polygm/cat_2022/images/5.2사진.jpg

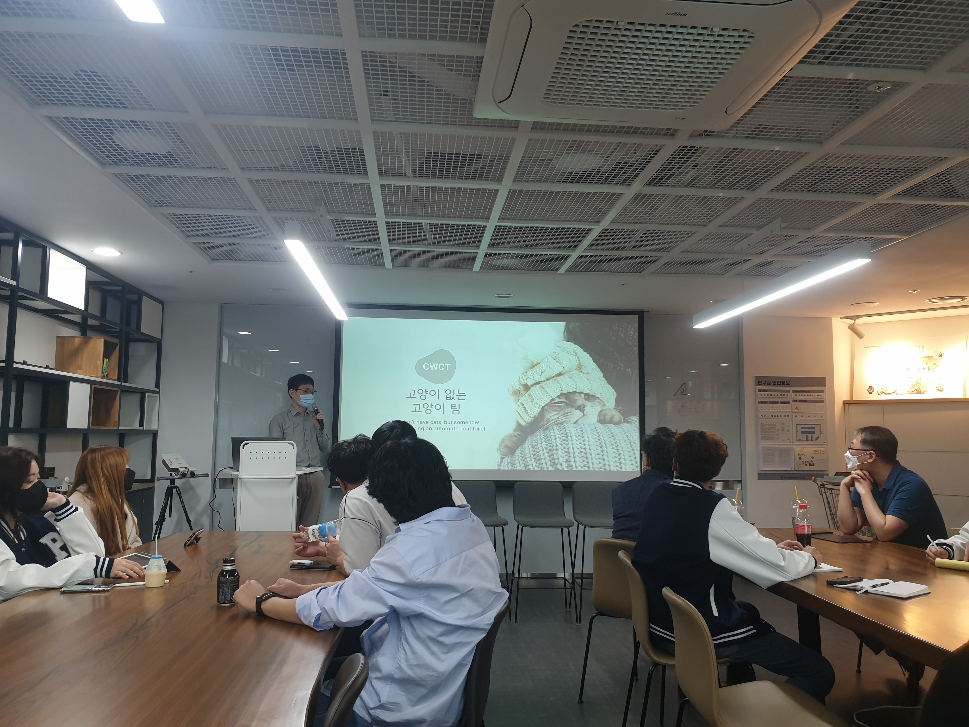
images/5.2사진.jpg
