polygm/cat_2022/images/KakaoTalk_20220418_165429345.png

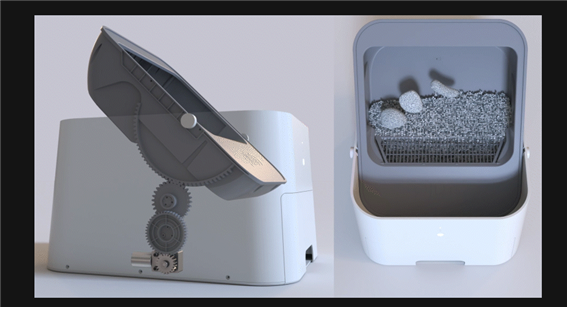
images/KakaoTalk_20220418_165429345.png
