polygm/cat_2022/images/KakaoTalk_20220705_105104796_04.jpg

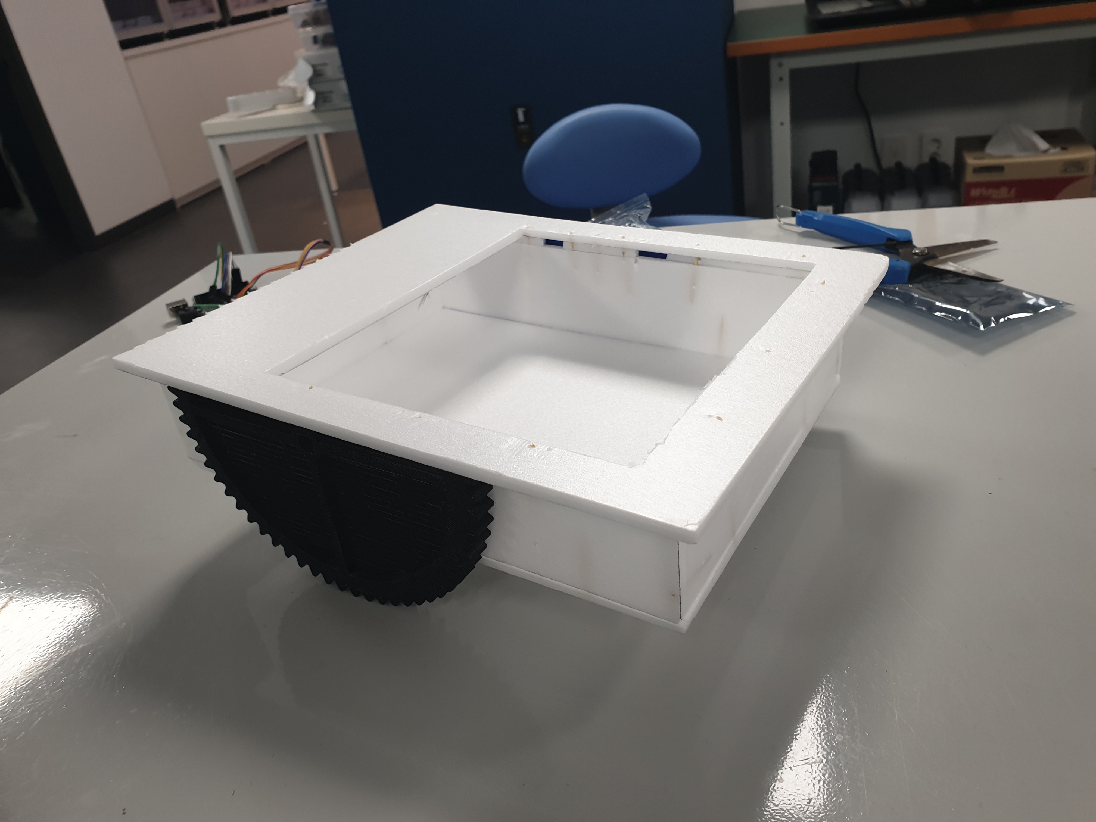
images/KakaoTalk_20220705_105104796_04.jpg
