polygm/cat_2022/images/KakaoTalk_20220705_162518360_03.jpg

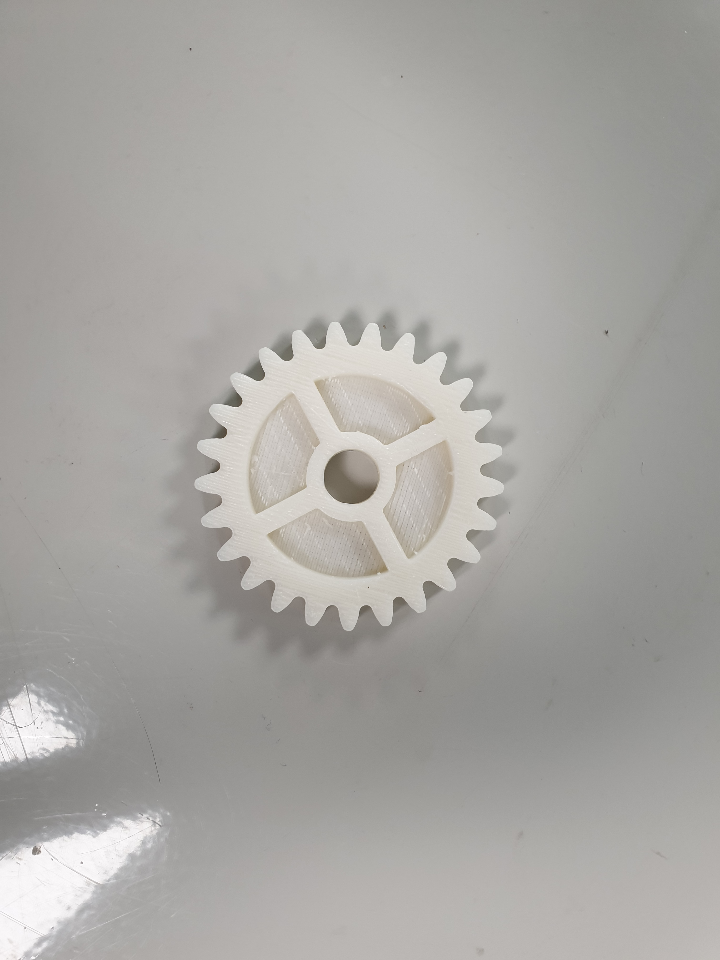
images/KakaoTalk_20220705_162518360_03.jpg
