polygm/cat_2022/images/KakaoTalk_20220920_115222162_04.jpg

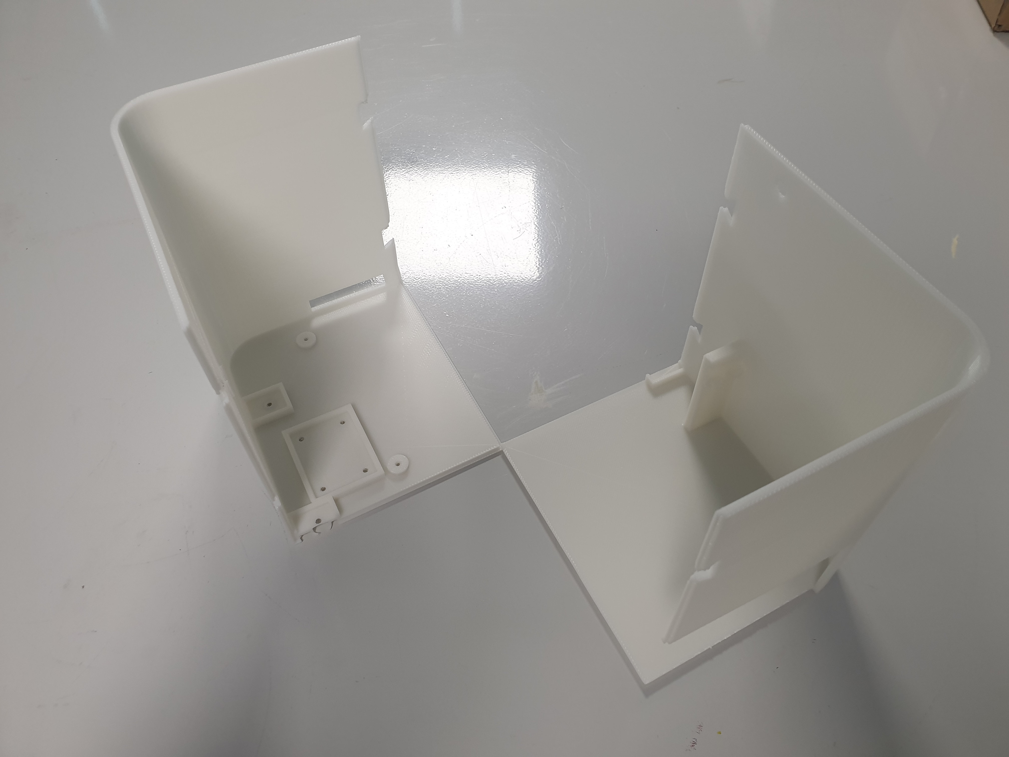
images/KakaoTalk_20220920_115222162_04.jpg
