polygm/cat_2022/images/KakaoTalk_20220922_130827342_01.jpg

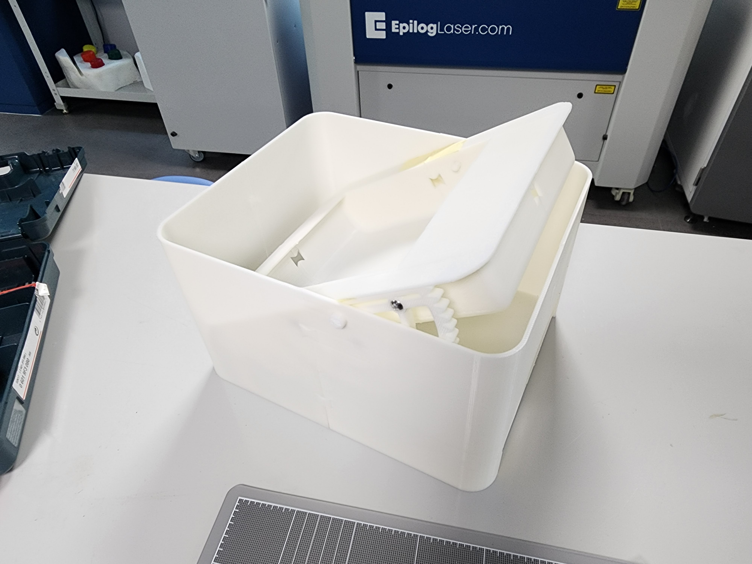
images/KakaoTalk_20220922_130827342_01.jpg
