polygm/cat_2022/images/KakaoTalk_20221005_131710617_01.jpg

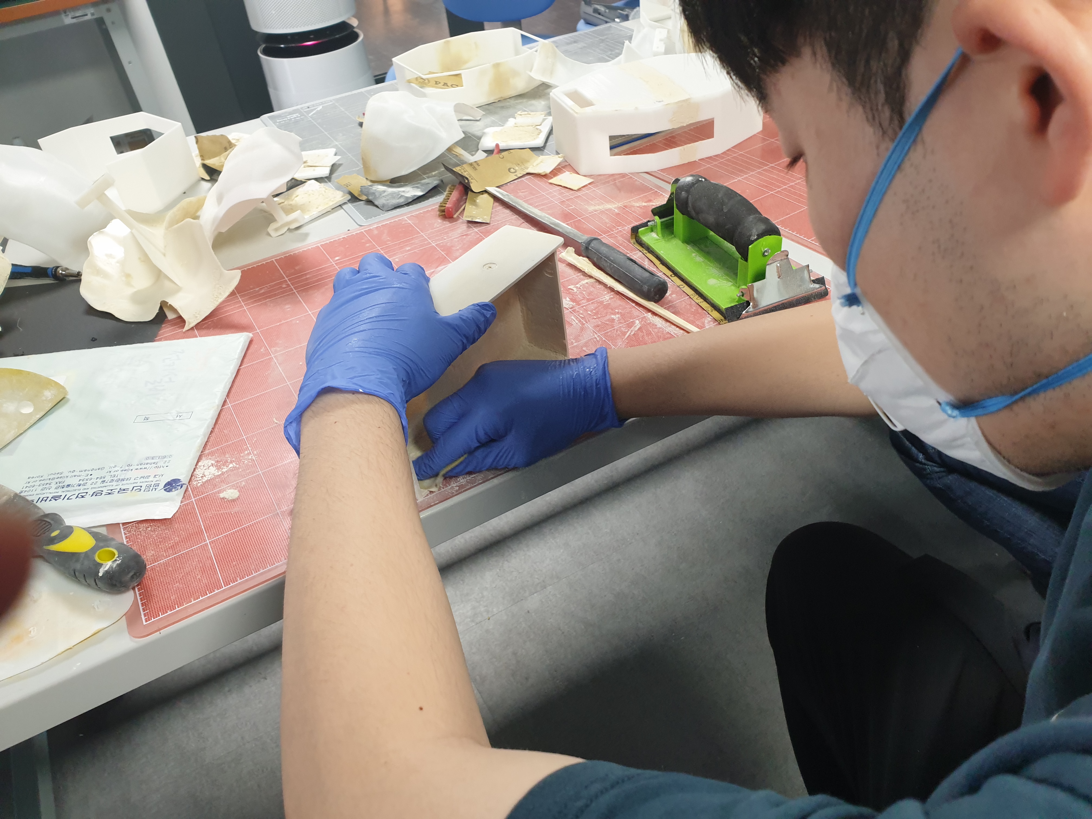
images/KakaoTalk_20221005_131710617_01.jpg
