polygm/cat_2022/images/KakaoTalk_20221005_131710617_03.jpg

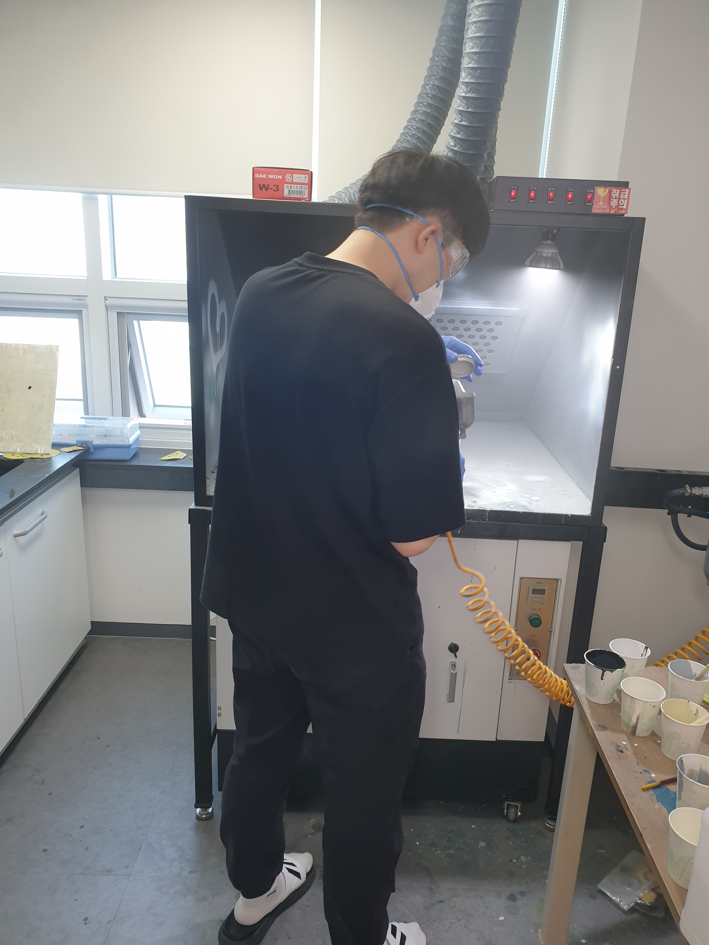
images/KakaoTalk_20221005_131710617_03.jpg
