polygm/cat_2022/images/KakaoTalk_20221005_131710617_04.jpg

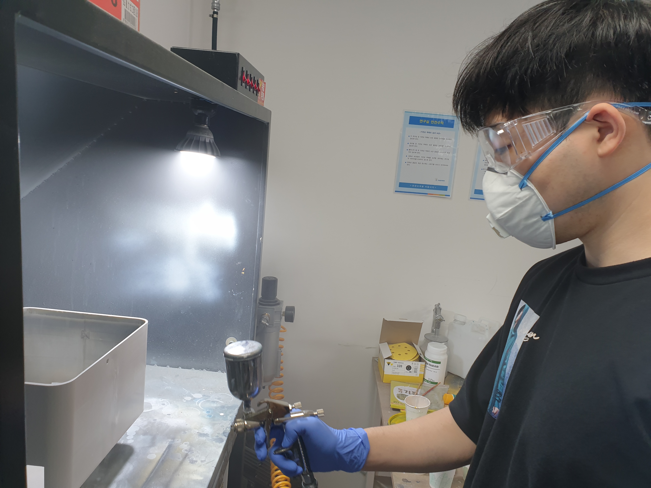
images/KakaoTalk_20221005_131710617_04.jpg
