polygm/cat_2022/images/발표.JPG

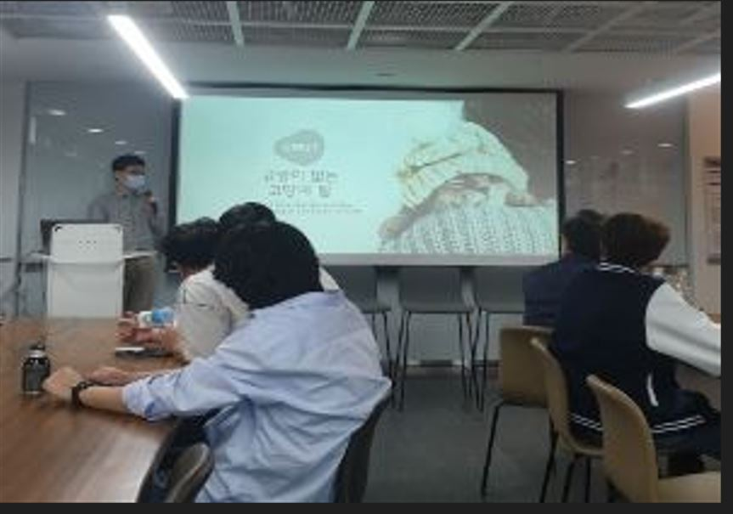
images/발표.JPG
