polygm/cat_2022/images/사전 회의.JPG

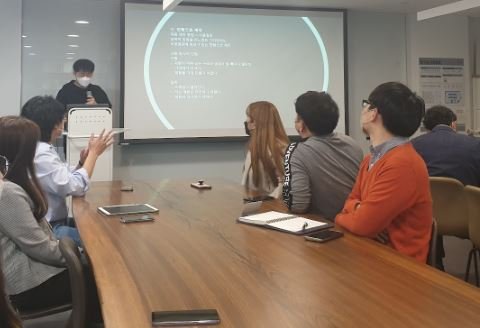
images/사전 회의.JPG
