polygm/cat_2022/images/사전.JPG

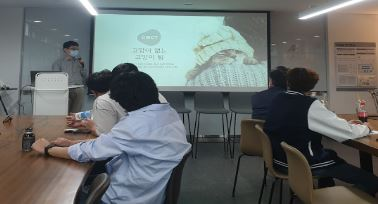
images/사전.JPG
