polygm/cat_2022/images/첫 모형 제작.jpg

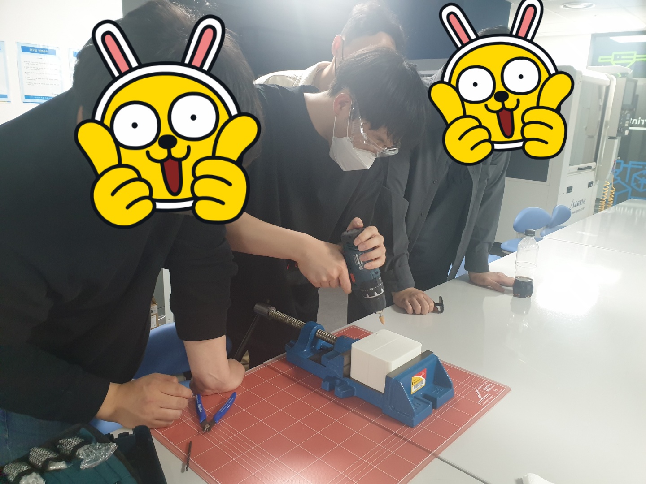
images/첫 모형 제작.jpg
