polygm/cat_2022/modeling/0.JPG

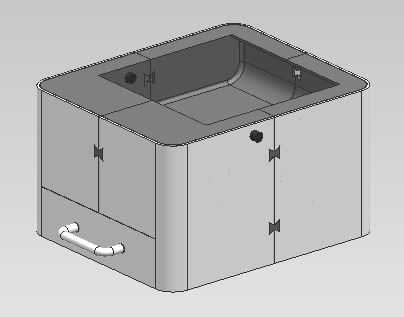
modeling/0.JPG
