polygm/cat_2022/modeling/CWCT특장점.JPG

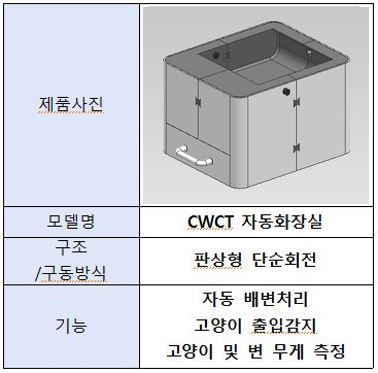
modeling/CWCT특장점.JPG
