polygm/cat_2022/modeling/고양이 분해도.png

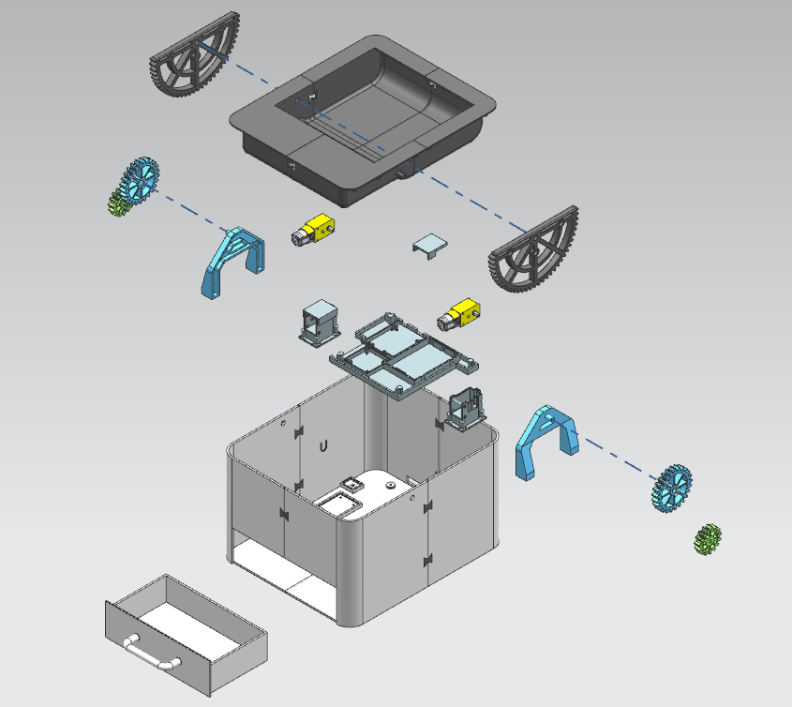
modeling/고양이 분해도.png
