polygm/cat_2022/modeling/기어1.JPG

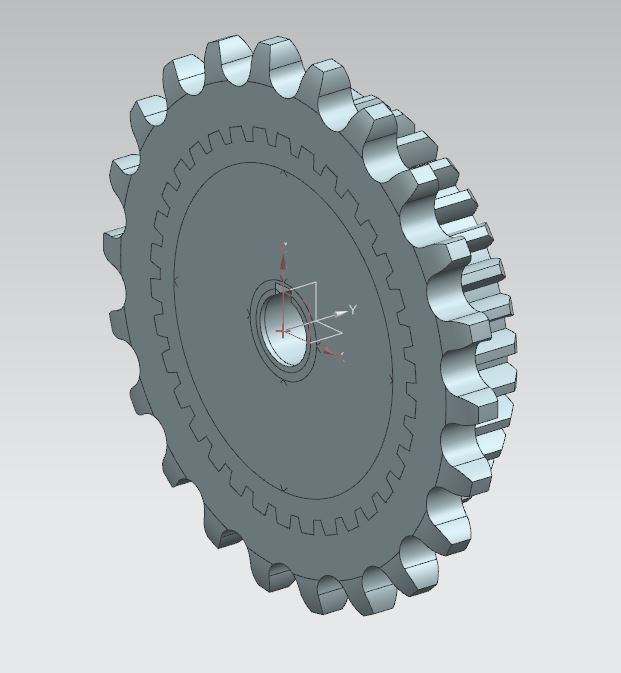
modeling/기어1.JPG
