polygm/cat_2022/modeling/기어2.JPG

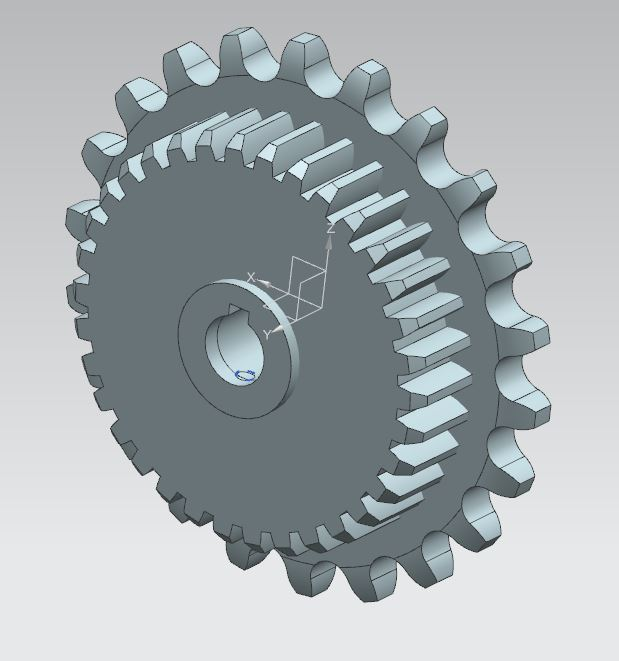
modeling/기어2.JPG
