polygm/cat_2022/modeling/기어3.JPG

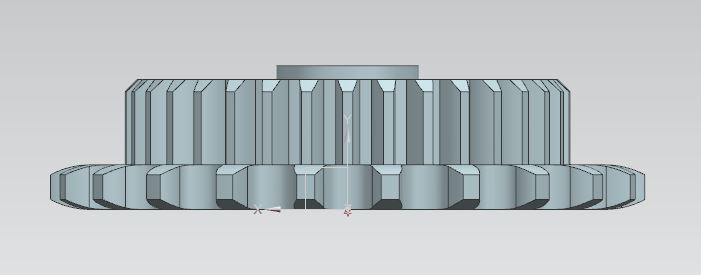
modeling/기어3.JPG
