polygm/cat_2022/modeling/기어4.JPG

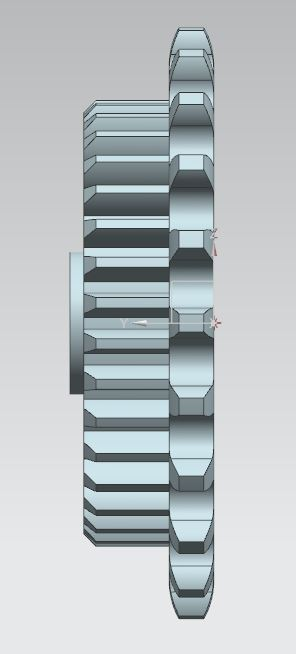
modeling/기어4.JPG
