polygm/cat_2022/modeling/모래통 기어.JPG

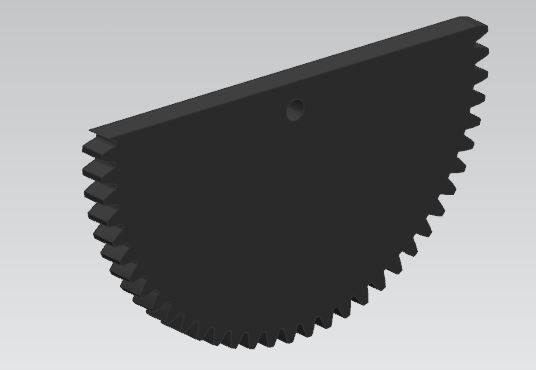
modeling/모래통 기어.JPG
