polygm/cat_2022/modeling/모래통 드래프팅.JPG

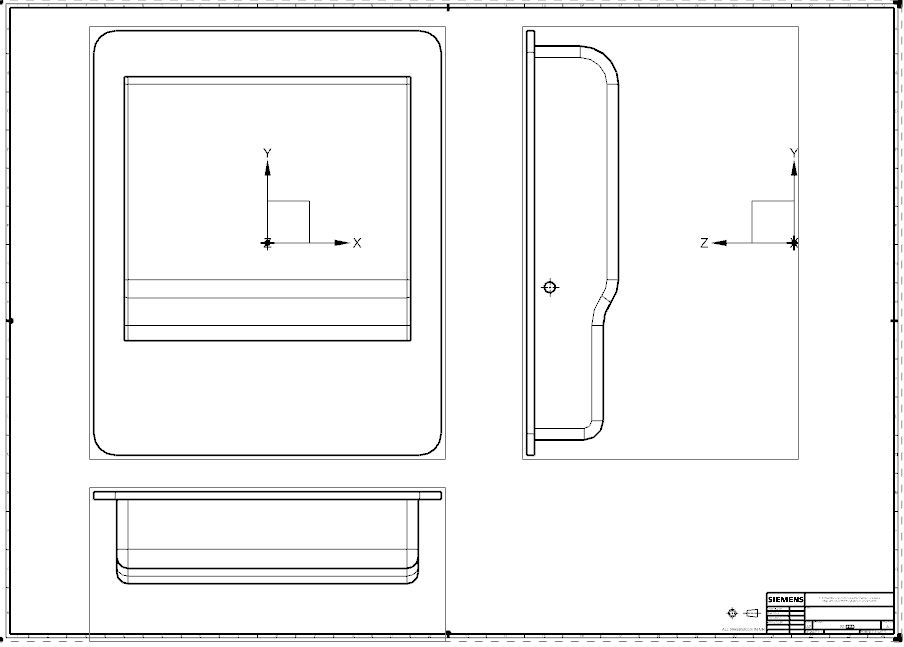
modeling/모래통 드래프팅.JPG
