polygm/cat_2022/modeling/본체 드래프팅.JPG

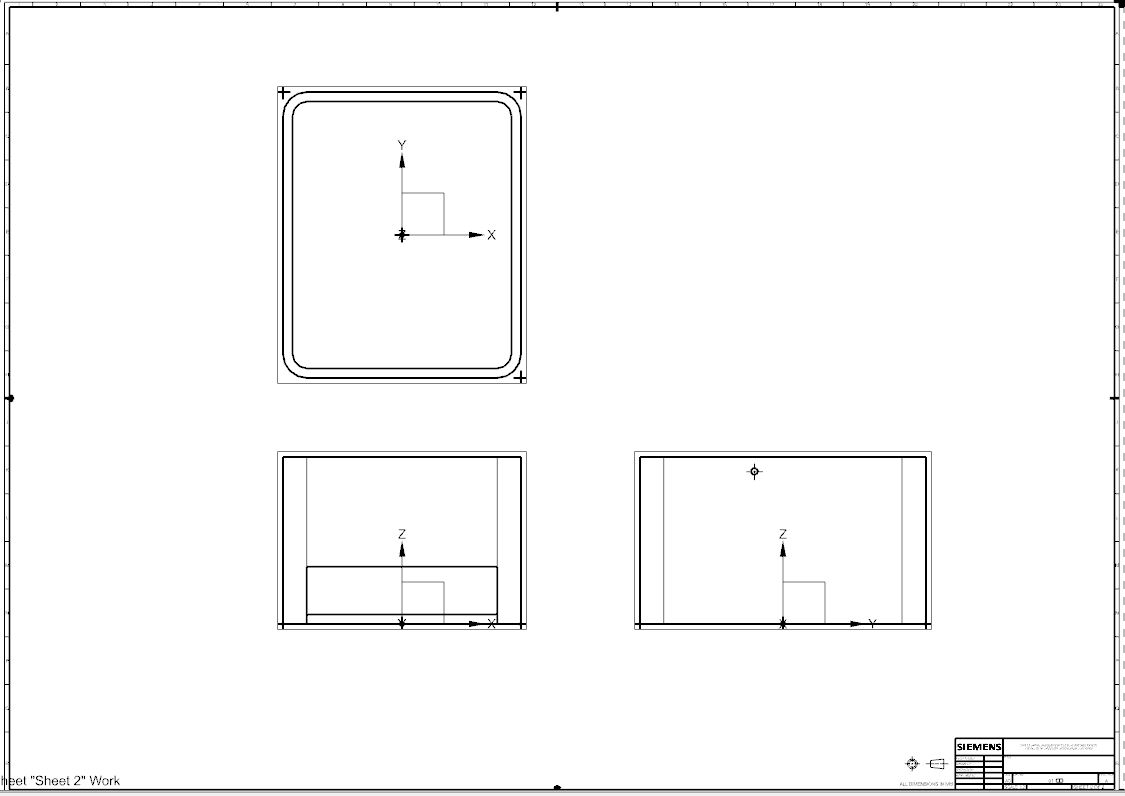
modeling/본체 드래프팅.JPG
