polygm/cat_2022/modeling/완성품1.png

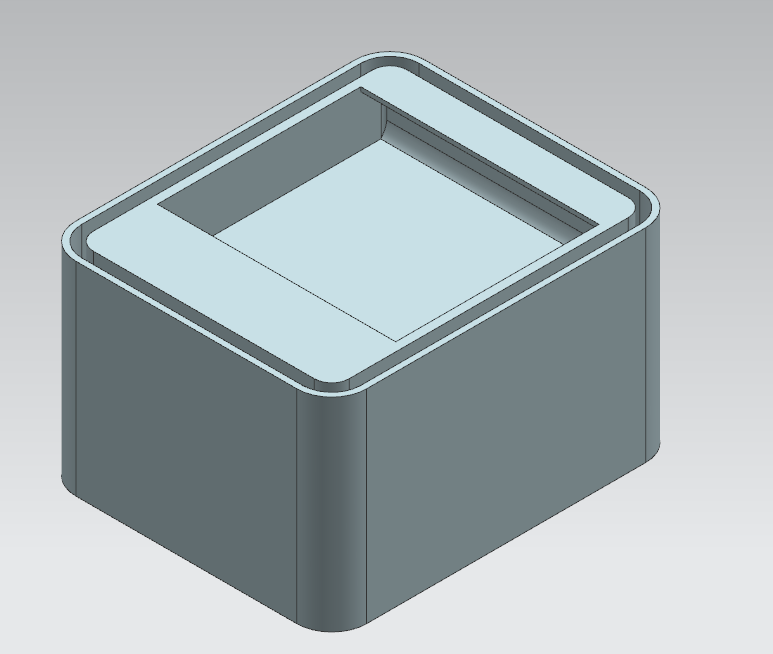
modeling/완성품1.png
