polygm/cat_2022/modeling/완성품2.png

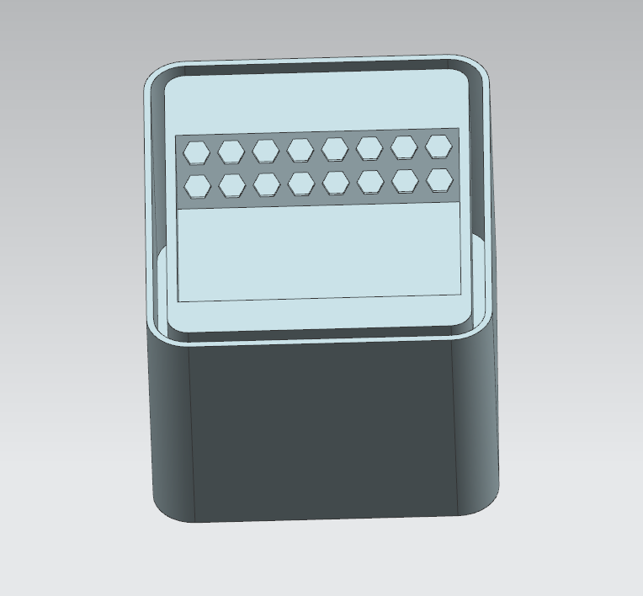
modeling/완성품2.png
