polygm/cat_2022/modeling/컴포넌트/ㅇ/Ultrasonic Sensor HC-SR04/Ultrasonic Sensor HC-SR04 2.jpg

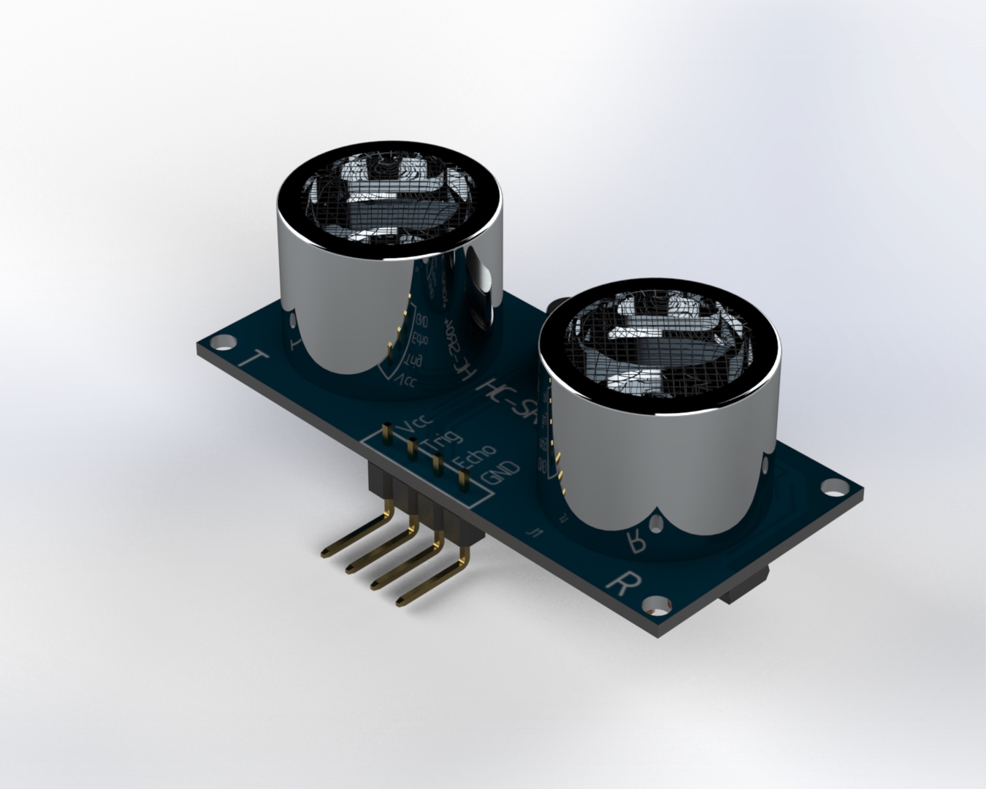
modeling/컴포넌트/ㅇ/Ultrasonic Sensor HC-SR04/Ultrasonic Sensor HC-SR04 2.jpg
