polygm/cat_2022/modeling/컴포넌트/두견/foto_4.png

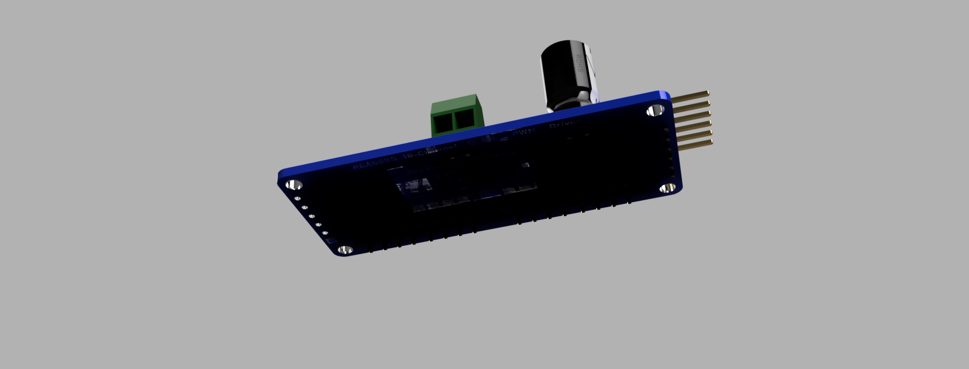
modeling/컴포넌트/두견/foto_4.png
