polygm/cat_2022/modeling/화장실 작동 순서 사진/2.JPG

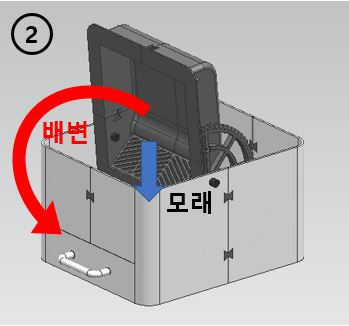
modeling/화장실 작동 순서 사진/2.JPG
