polygm/cat_2022/modeling/회전부.png

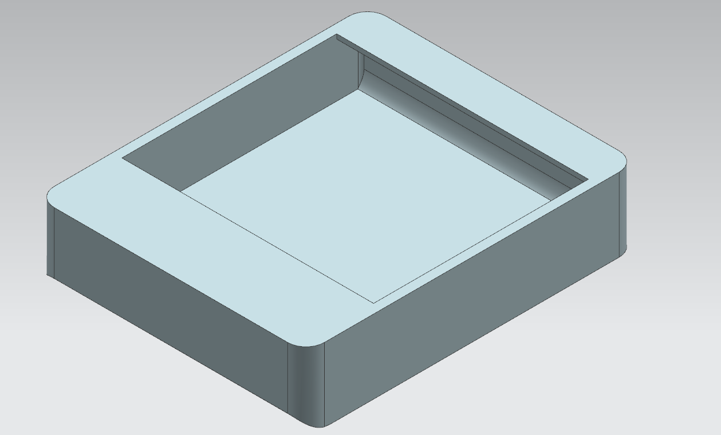
modeling/회전부.png
