polygm/cat_2022/product/KakaoTalk_20221005_114139845.jpg

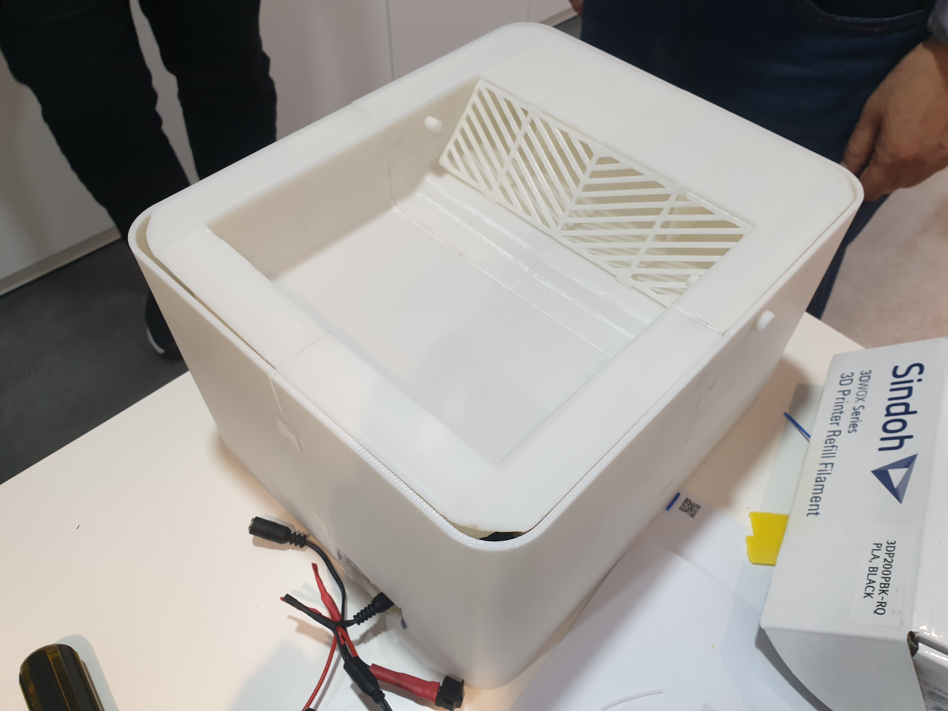
product/KakaoTalk_20221005_114139845.jpg
