polygm/cat_2022/product/KakaoTalk_20221005_131516674_01.jpg

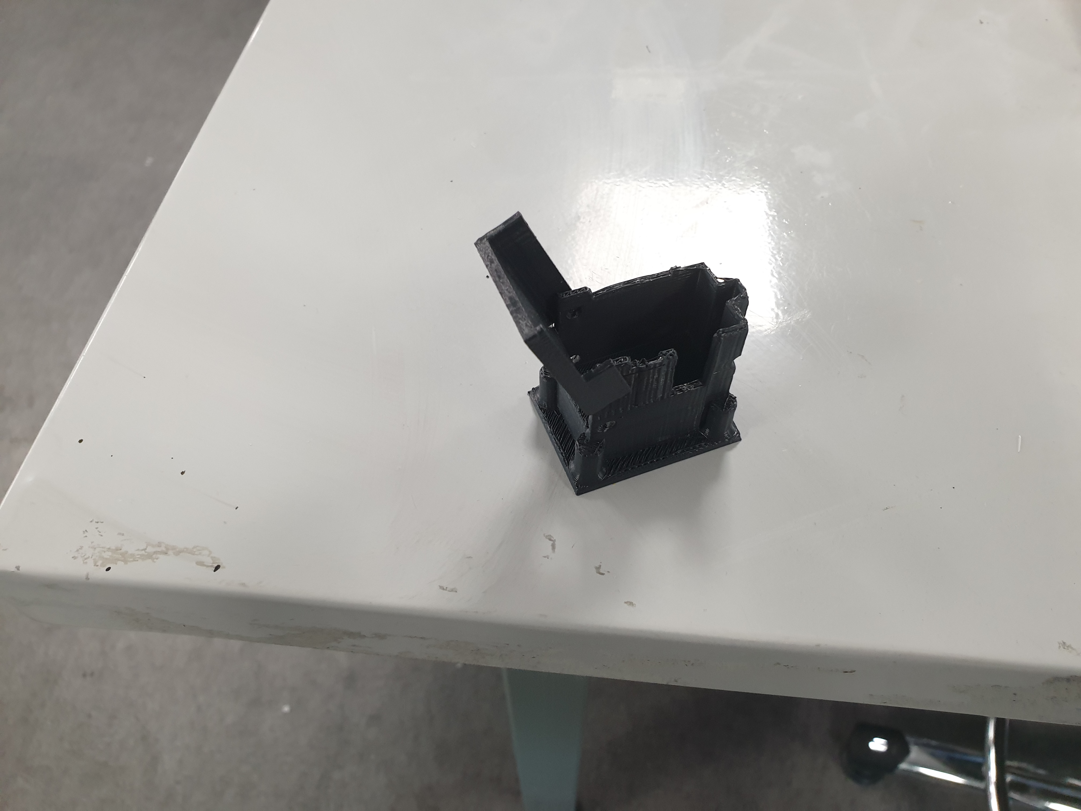
product/KakaoTalk_20221005_131516674_01.jpg
