polygm/cat_2022/product/KakaoTalk_20221005_131516674_02.jpg

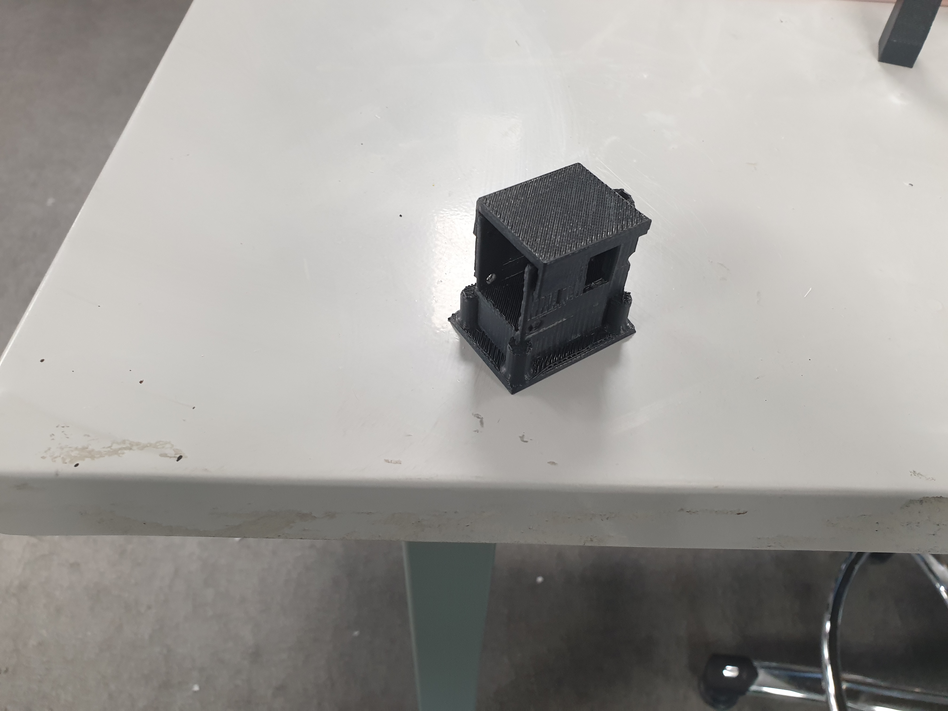
product/KakaoTalk_20221005_131516674_02.jpg
