polygm/cat_2022/product/KakaoTalk_20221005_131516674_05.jpg

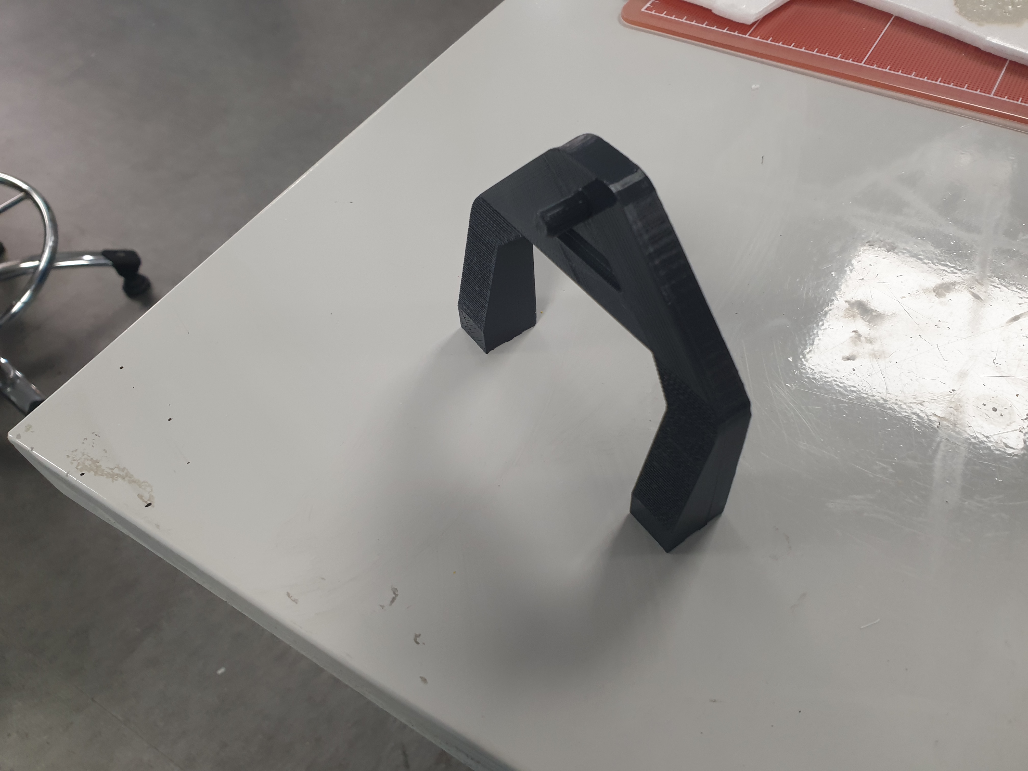
product/KakaoTalk_20221005_131516674_05.jpg
