polygm/cat_2022/product/KakaoTalk_20221005_131516674_07.jpg

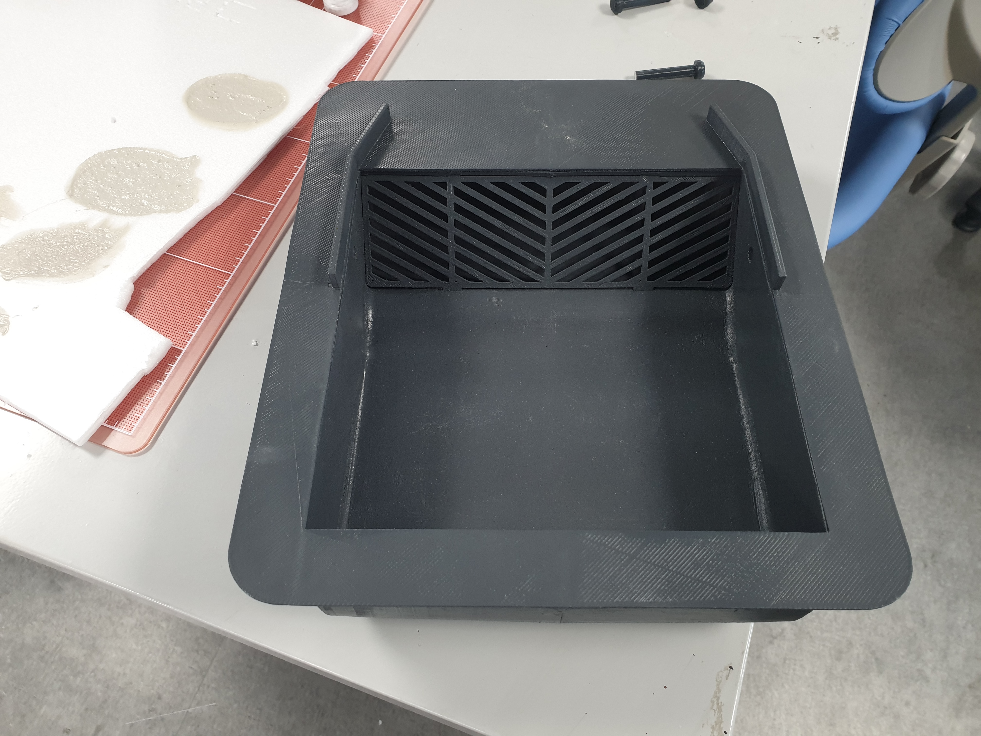
product/KakaoTalk_20221005_131516674_07.jpg
