polygm/cat_2022/research/4.JPG

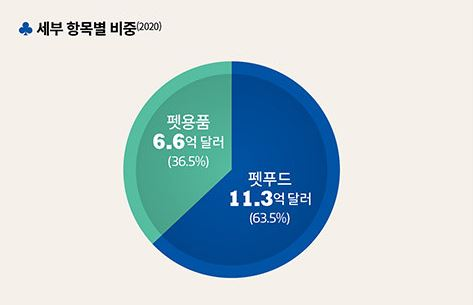
research/4.JPG
