polygm/cat_2022/research/5.JPG

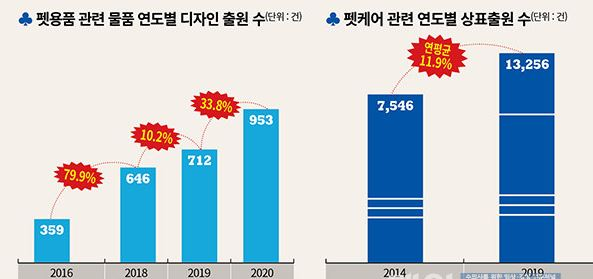
research/5.JPG
