polygm/cat_2022/research/7.JPG

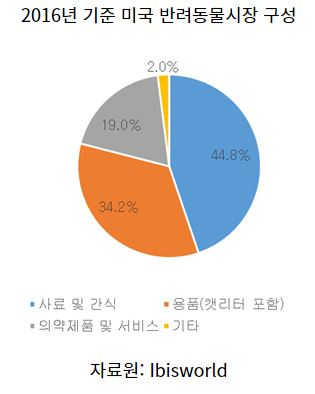
research/7.JPG
