polygm/cat_2022/research/8.JPG

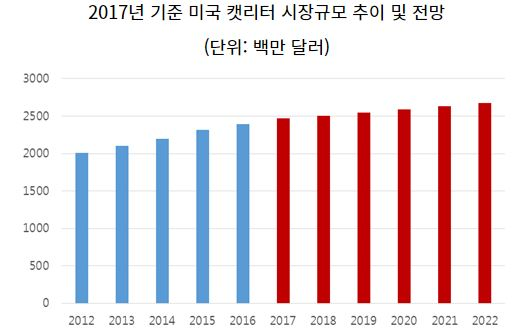
research/8.JPG
