polygm/cat_2022/research/3213.JPG

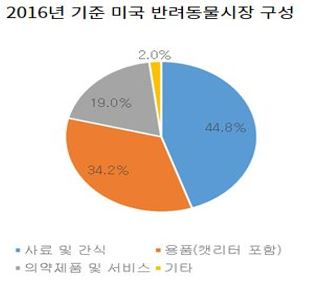
research/3213.JPG
