polygm/cat_2022/research/cheap.JPG

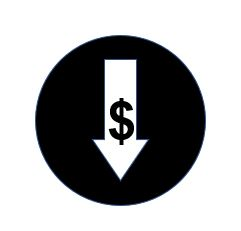
research/cheap.JPG
