polygm/cat_2022/research/cheaper.JPG

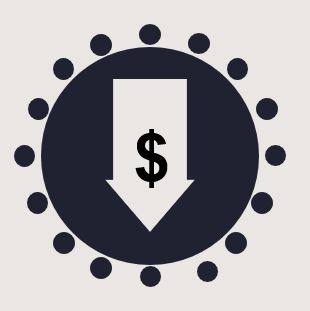
research/cheaper.JPG
