polygm/cat_2022/research/g.jpg

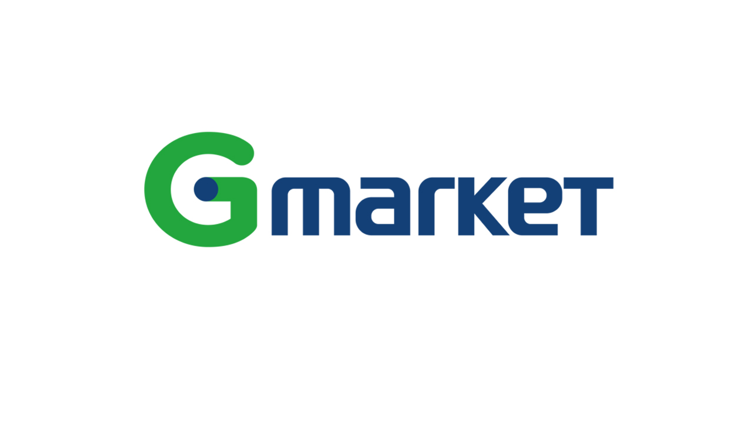
research/g.jpg
