polygm/cat_2022/research/gg.jpg

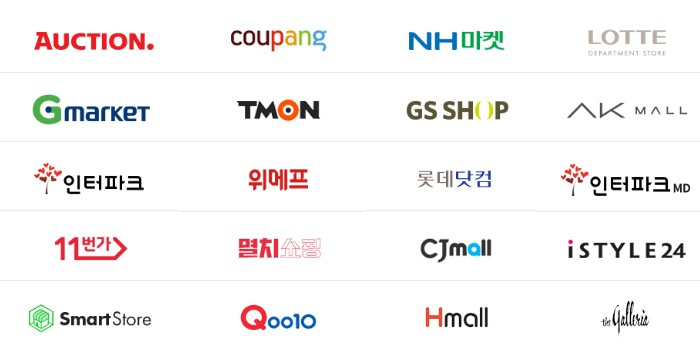
research/gg.jpg
