polygm/cat_2022/research/KakaoTalk_20220704_164942398.jpg

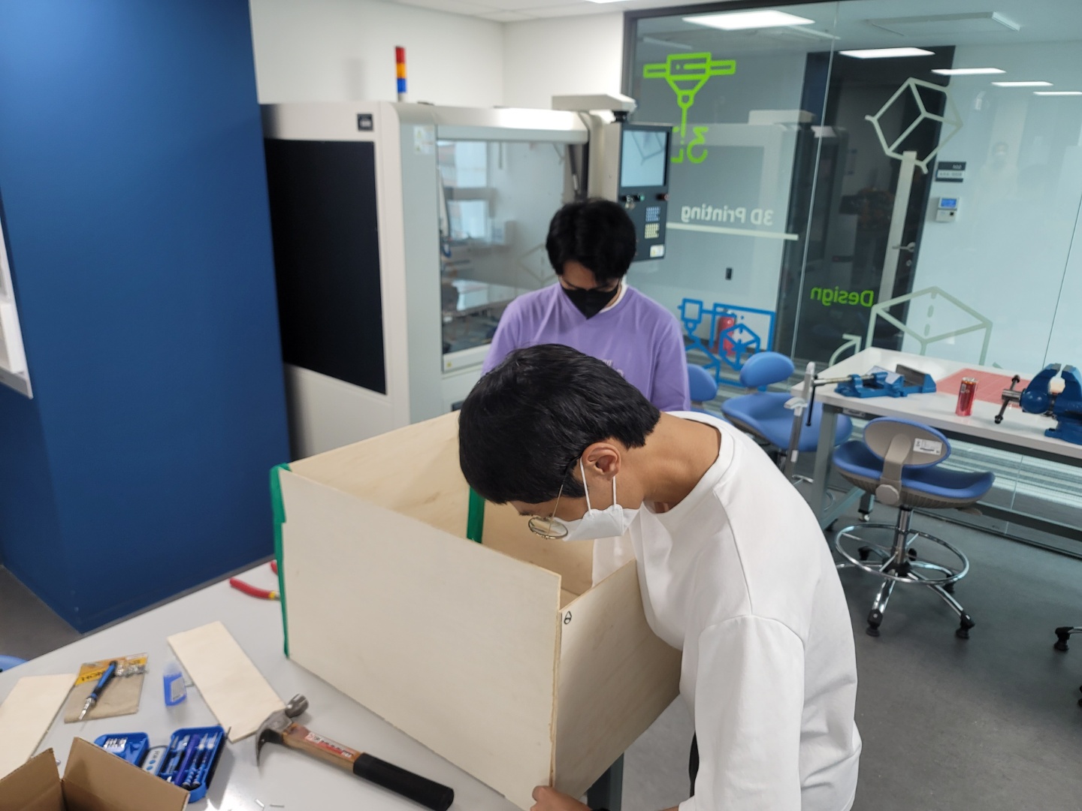
research/KakaoTalk_20220704_164942398.jpg
