polygm/cat_2022/research/KakaoTalk_20220920_115222162_03.jpg

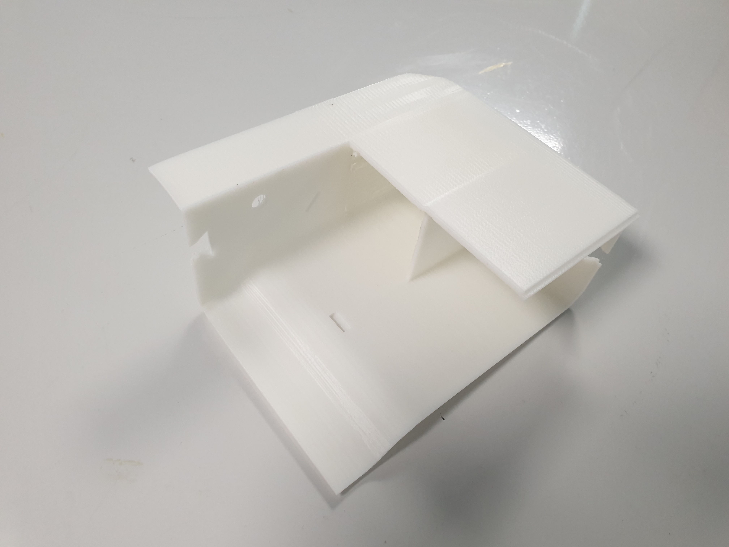
research/KakaoTalk_20220920_115222162_03.jpg
