polygm/cat_2022/research/KakaoTalk_20220922_152420083.png

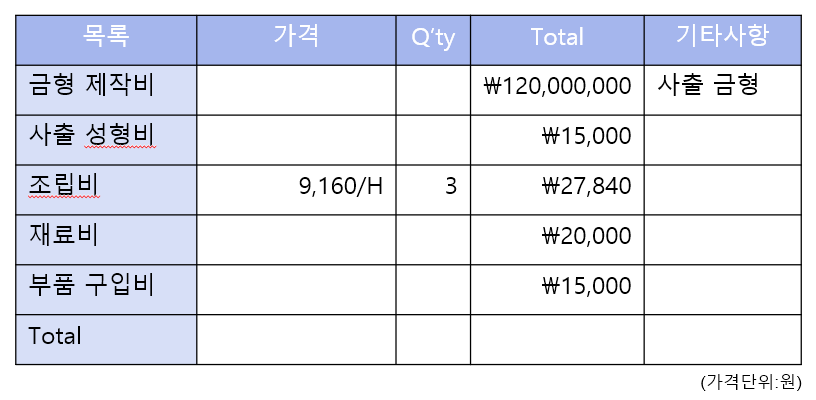
research/KakaoTalk_20220922_152420083.png
