polygm/cat_2022/research/s.JPG

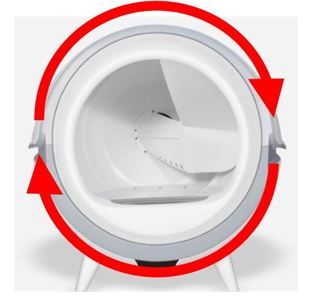
research/s.JPG
