polygm/cat_2022/research/Untitled-1.png

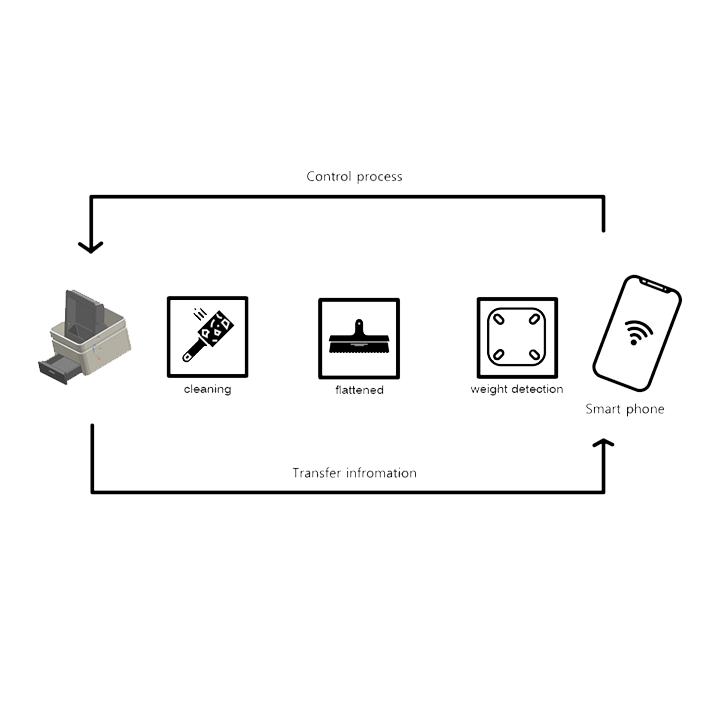
research/Untitled-1.png
