polygm/cat_2022/research/wifi모듈.JPG

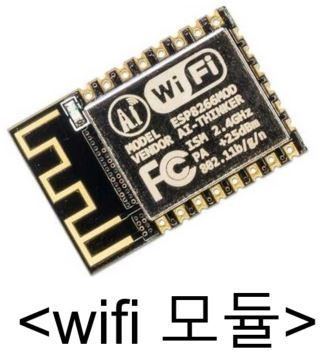
research/wifi모듈.JPG
