polygm/cat_2022/research/ㄴ.JPG

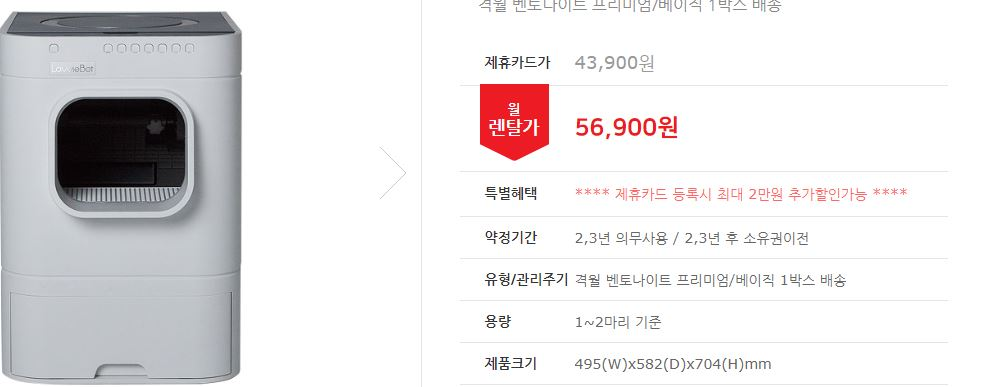
research/ㄴ.JPG
