polygm/cat_2022/research/개선.JPG

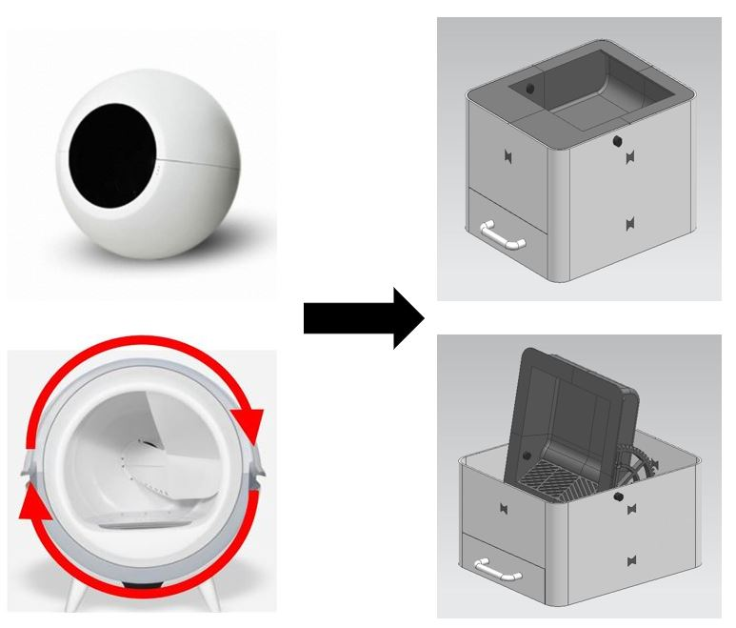
research/개선.JPG
