polygm/cat_2022/research/고양2.JPG

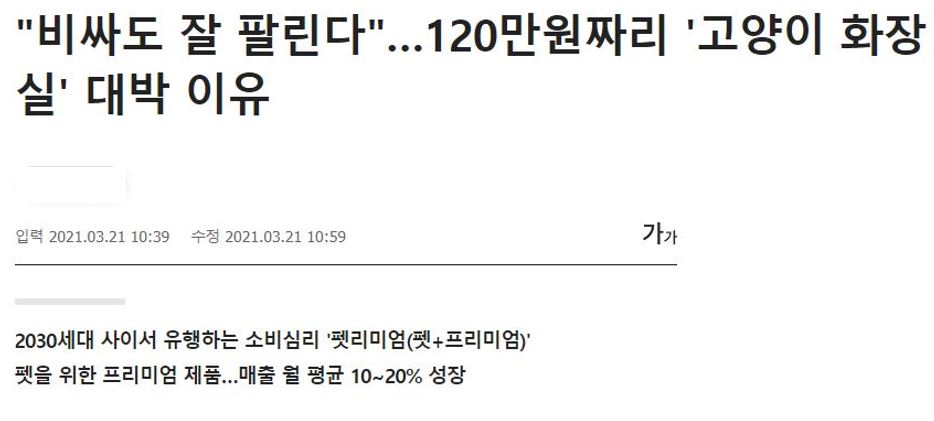
research/고양2.JPG
