polygm/cat_2022/research/고양.JPG

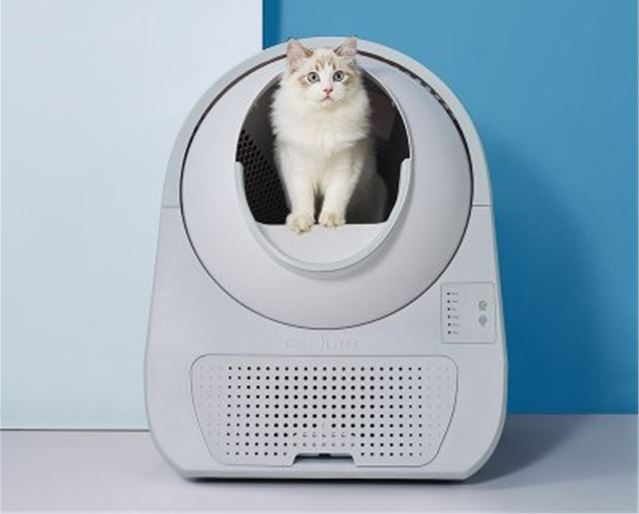
research/고양.JPG
