polygm/cat_2022/research/고양이2.jpg

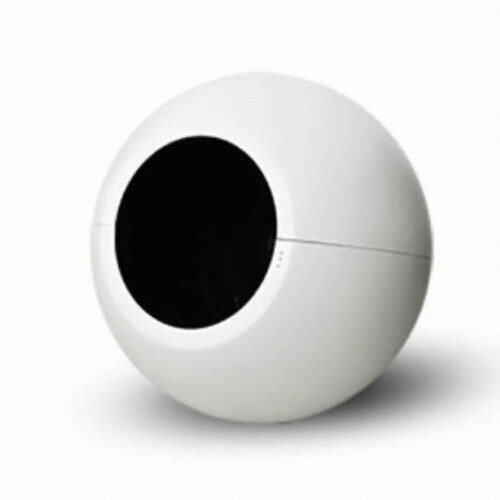
research/고양이2.jpg
