polygm/cat_2022/research/고양이 무게2.JPG

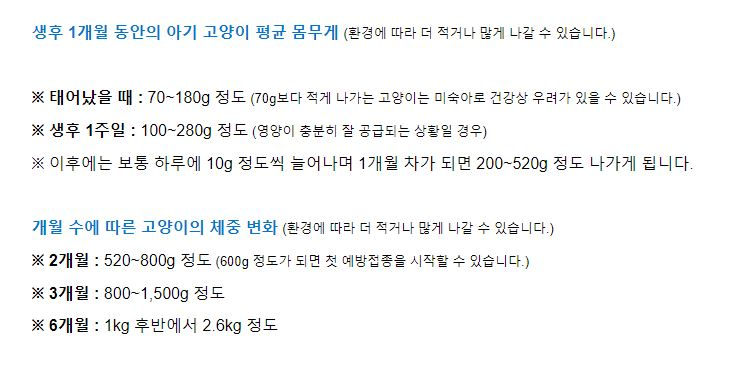
research/고양이 무게2.JPG
