polygm/cat_2022/research/고양이 시장2.JPG

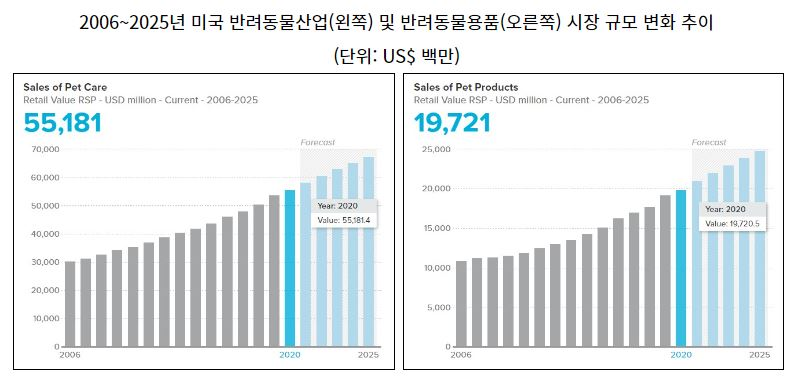
research/고양이 시장2.JPG
