polygm/cat_2022/research/고양이 시장규모.JPG

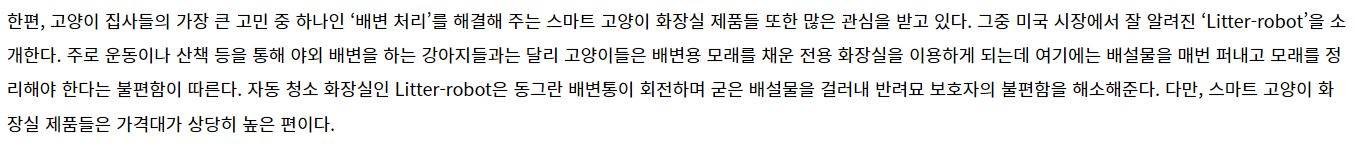
research/고양이 시장규모.JPG
