polygm/cat_2022/research/고양이 평균 무게.JPG

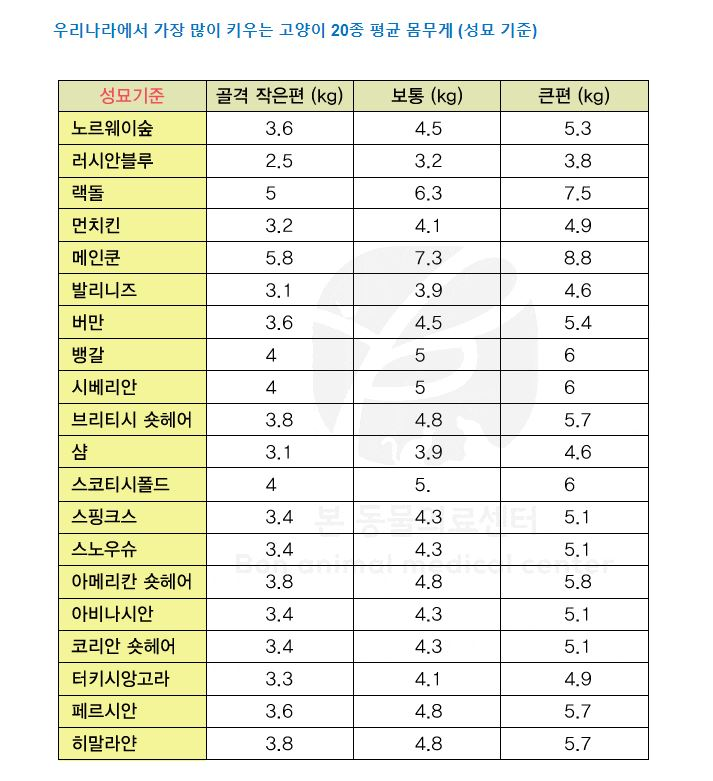
research/고양이 평균 무게.JPG
