polygm/cat_2022/research/구동도.JPG

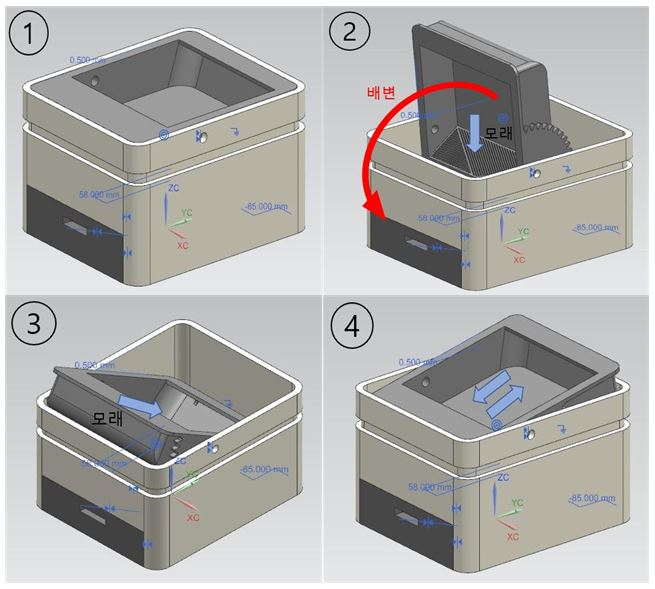
research/구동도.JPG
