polygm/cat_2022/research/구성도 완성.jpg

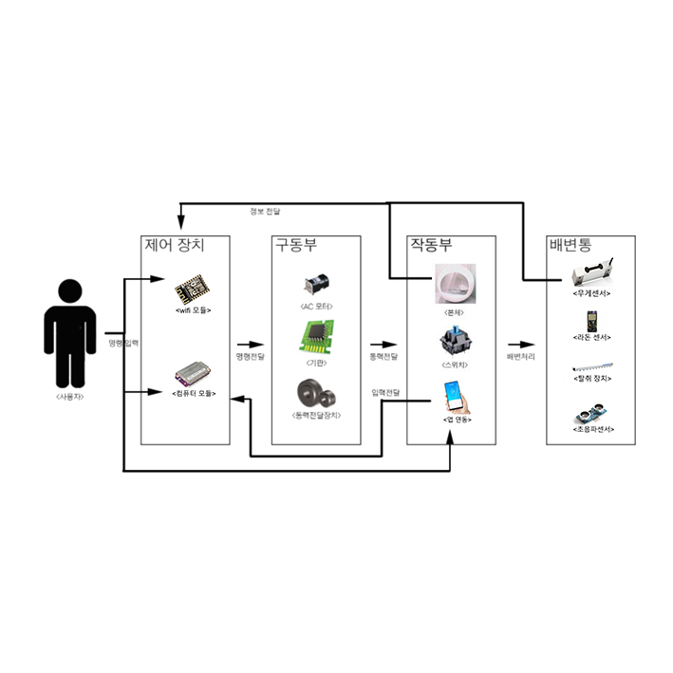
research/구성도 완성.jpg
