polygm/cat_2022/research/기능 흐름도.JPG

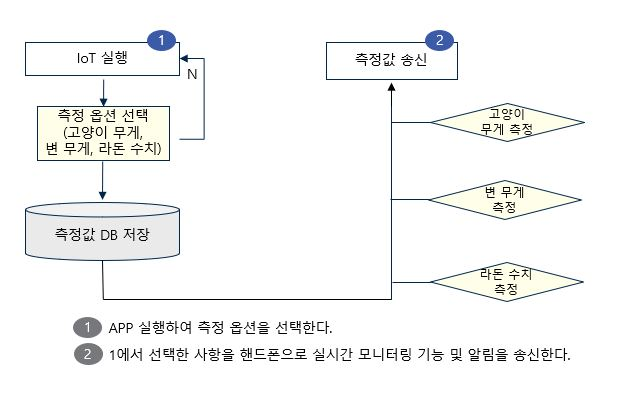
research/기능 흐름도.JPG
