polygm/cat_2022/research/기능처리.JPG

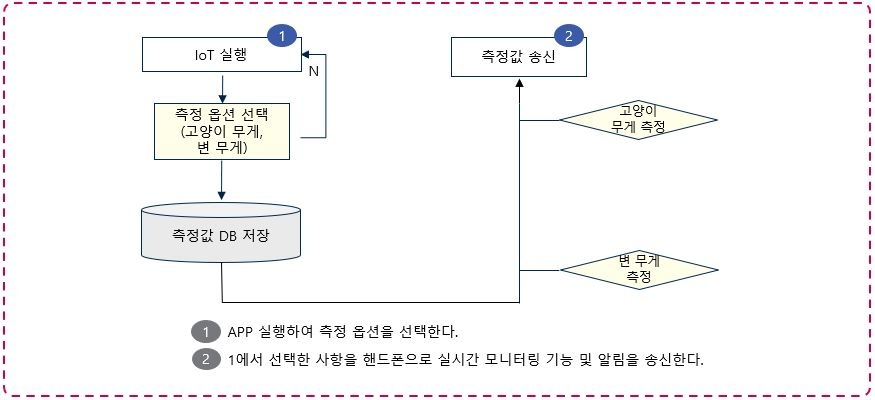
research/기능처리.JPG
