polygm/cat_2022/research/기어 설명.JPG

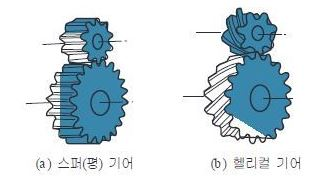
research/기어 설명.JPG
