polygm/cat_2022/research/냥장실 비교.JPG

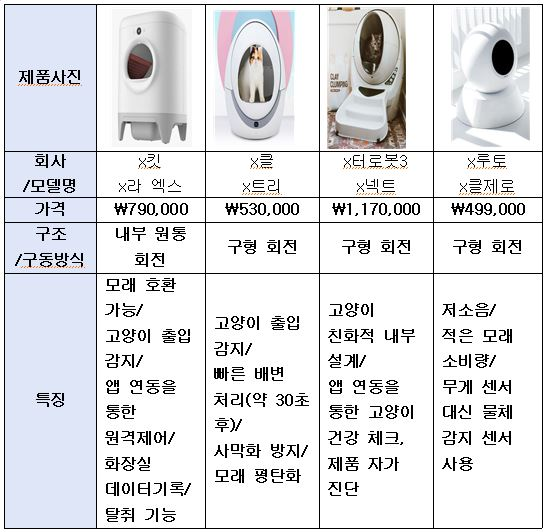
research/냥장실 비교.JPG
