polygm/cat_2022/research/라돈 센서.JPG

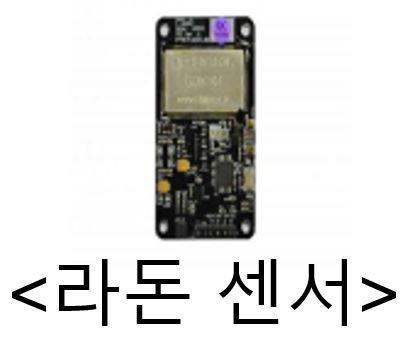
research/라돈 센서.JPG
