polygm/cat_2022/research/라돈센서.JPG

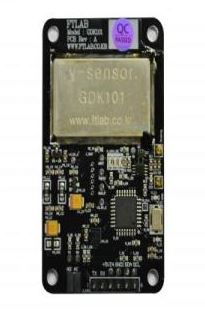
research/라돈센서.JPG
