polygm/cat_2022/research/모터 차이.JPG

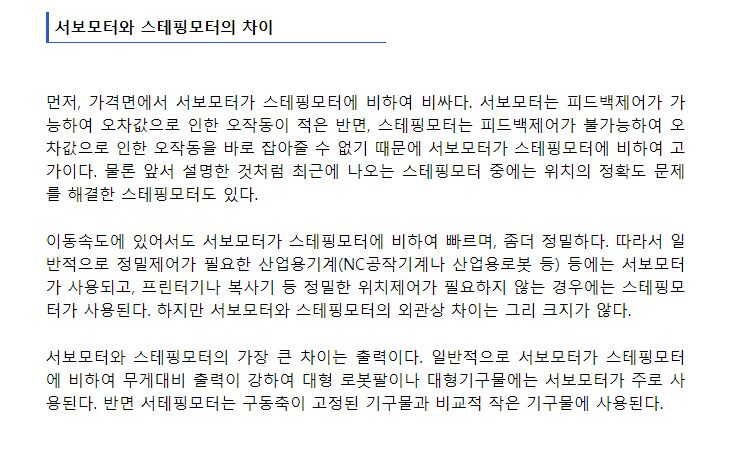
research/모터 차이.JPG
