polygm/cat_2022/research/모터.JPG

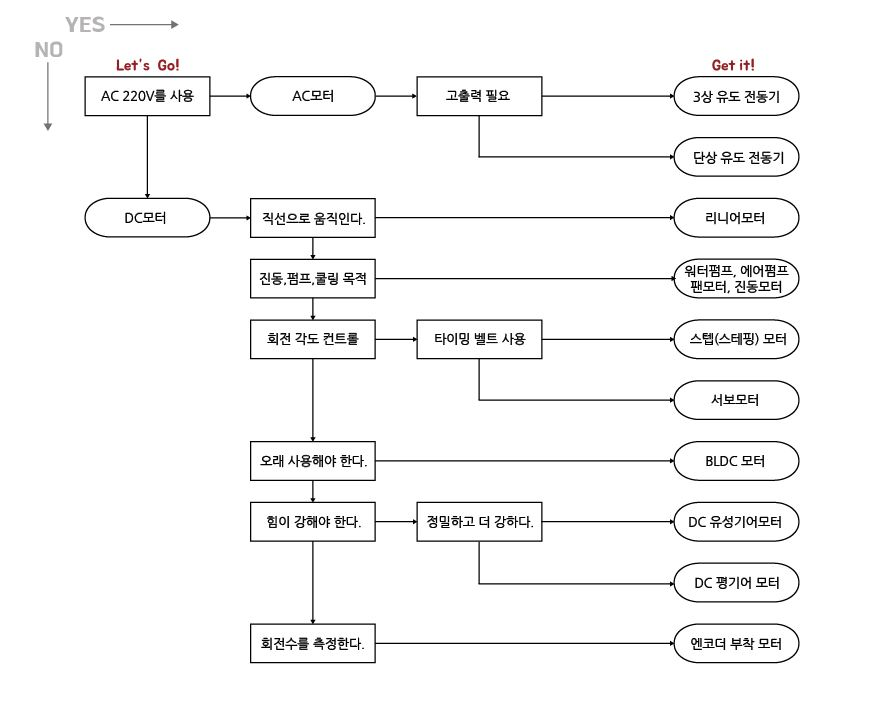
research/모터.JPG
