polygm/cat_2022/research/무게 센서 사진.JPG

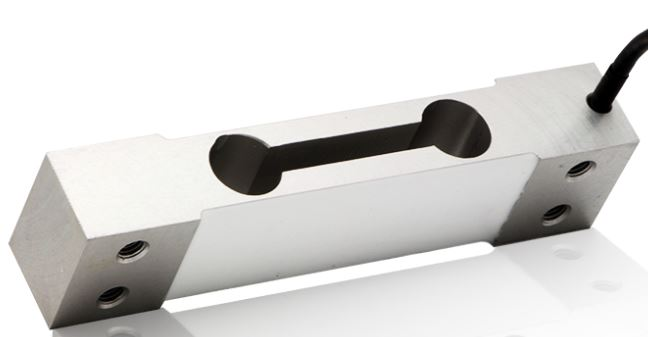
research/무게 센서 사진.JPG
