polygm/cat_2022/research/무게센서.JPG

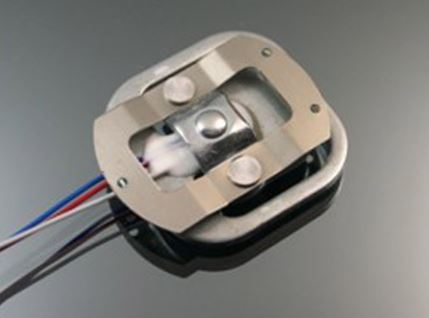
research/무게센서.JPG
