polygm/cat_2022/research/반려 희망.JPG

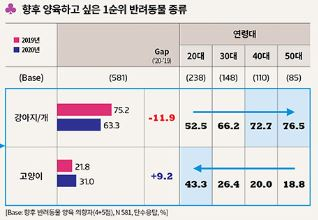
research/반려 희망.JPG
