polygm/cat_2022/research/반려동물 애로사항.JPG

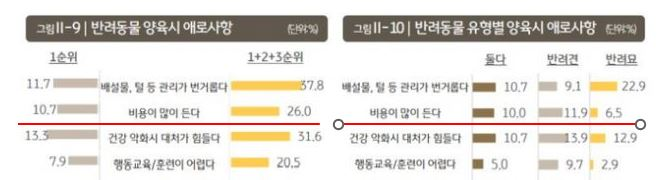
research/반려동물 애로사항.JPG
