polygm/cat_2022/research/반려동물 연령대.JPG

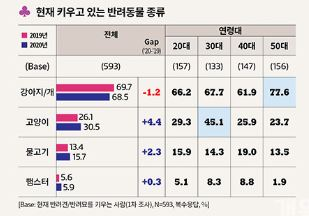
research/반려동물 연령대.JPG
