polygm/cat_2022/research/반려묘.JPG

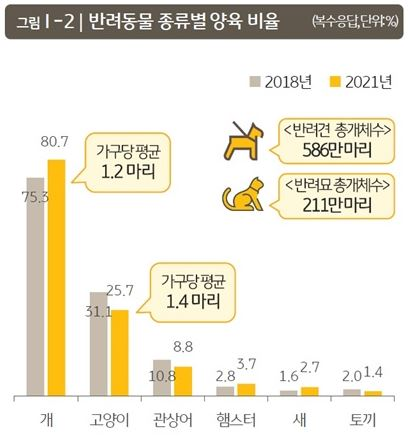
research/반려묘.JPG
