polygm/cat_2022/research/반자동.JPG

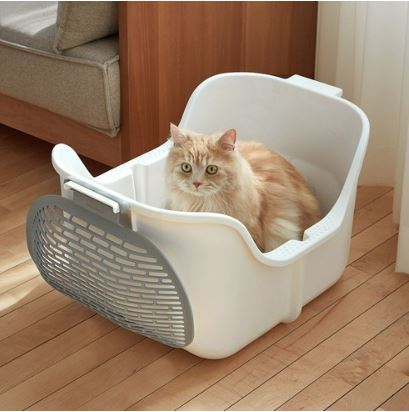
research/반자동.JPG
