polygm/cat_2022/research/본체(동영상용).JPG

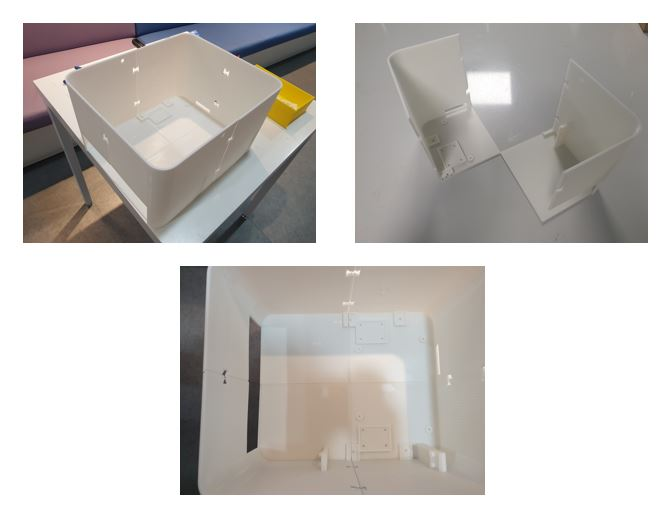
research/본체(동영상용).JPG
