polygm/cat_2022/research/부속.JPG

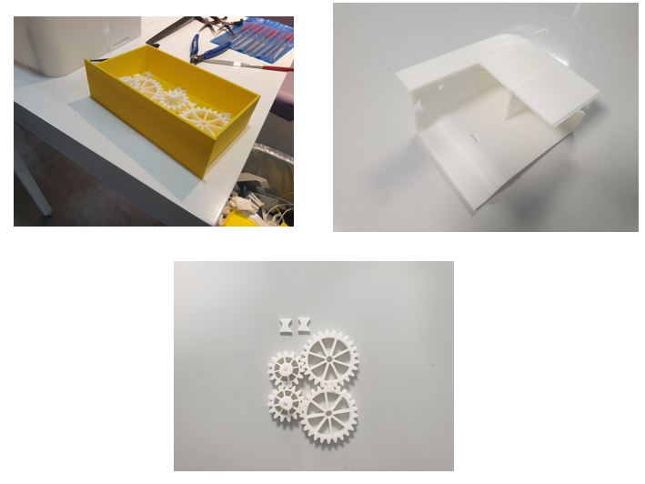
research/부속.JPG
