polygm/cat_2022/research/스텝모터.JPG

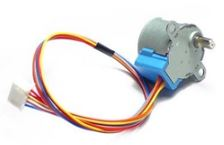
research/스텝모터.JPG
