polygm/cat_2022/research/스퍼-헬리퍼 차이.JPG

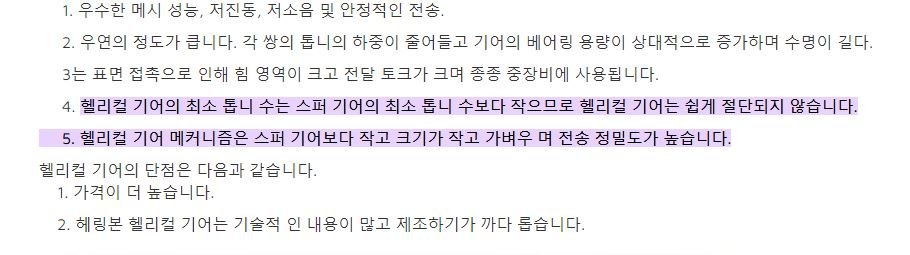
research/스퍼-헬리퍼 차이.JPG
