polygm/cat_2022/research/시장크기.JPG

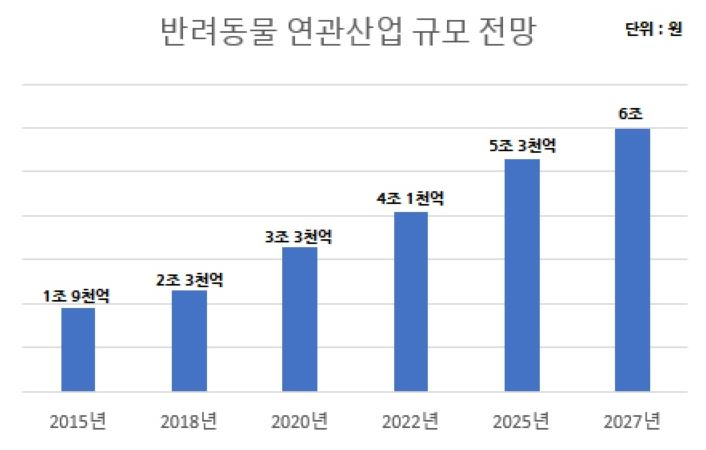
research/시장크기.JPG
