polygm/cat_2022/research/앱 연동.JPG

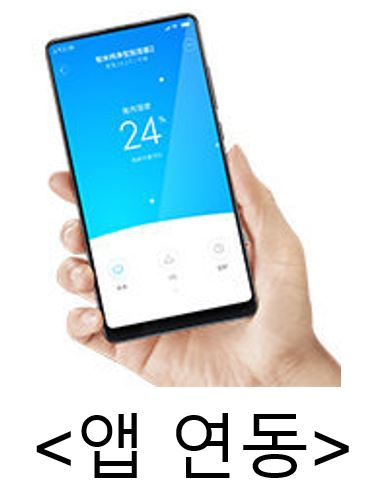
research/앱 연동.JPG
