polygm/cat_2022/research/양육 시 애로사항.JPG

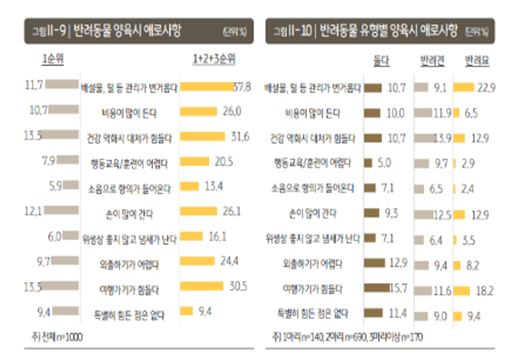
research/양육 시 애로사항.JPG
