polygm/cat_2022/research/양육 현황.JPG

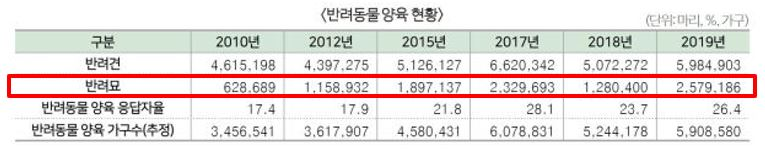
research/양육 현황.JPG
