polygm/cat_2022/research/에프티랩 라돈센서.JPG

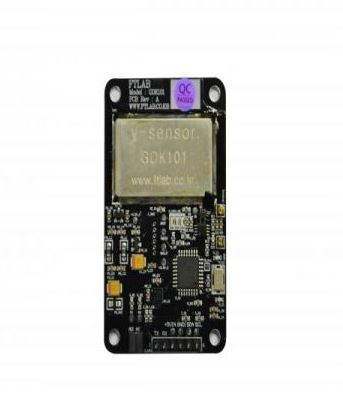
research/에프티랩 라돈센서.JPG
