polygm/cat_2022/research/원형 화장실.JPG

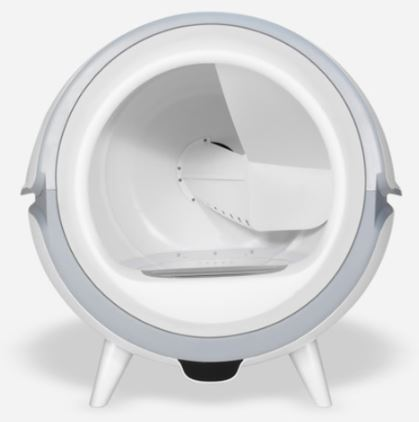
research/원형 화장실.JPG
