polygm/cat_2022/research/창업지원한도.JPG

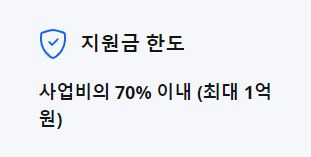
research/창업지원한도.JPG
