polygm/cat_2022/research/청년창업지원금.JPG

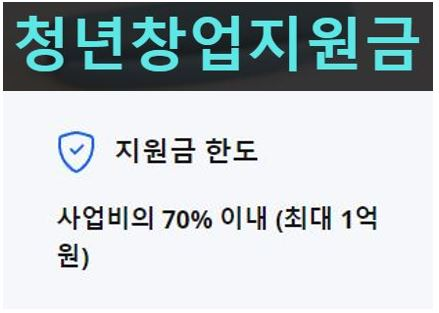
research/청년창업지원금.JPG
