polygm/cat_2022/research/초음파센서.JPG

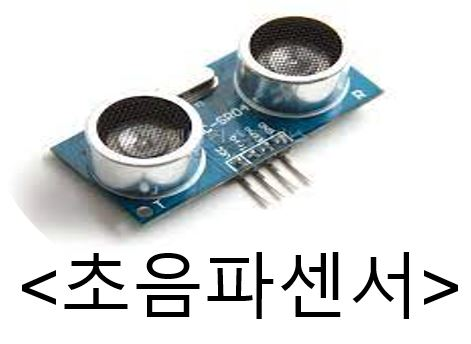
research/초음파센서.JPG
