polygm/cat_2022/research/캡처2.JPG

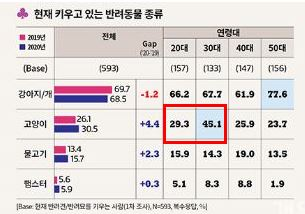
research/캡처2.JPG
