polygm/cat_2022/research/캡처.JPG

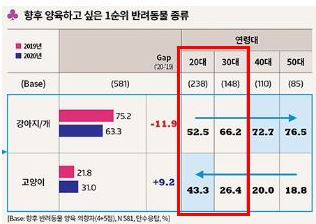
research/캡처.JPG
