polygm/cat_2022/research/컴모듈.JPG

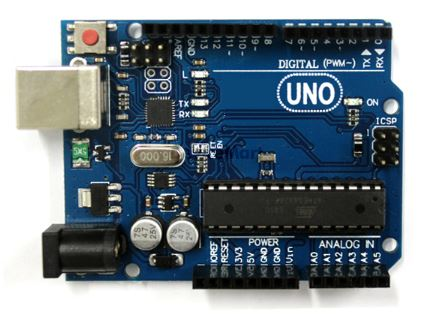
research/컴모듈.JPG
