polygm/cat_2022/research/컴퓨터모듈.JPG

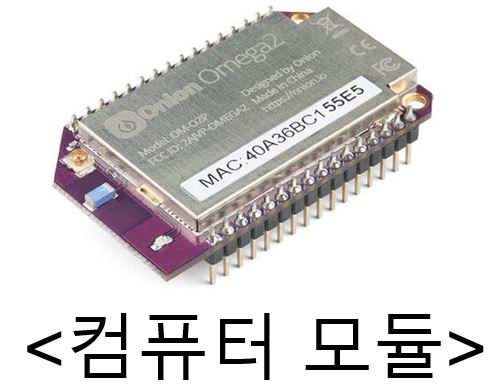
research/컴퓨터모듈.JPG
