polygm/cat_2022/research/탈취 장치.JPG

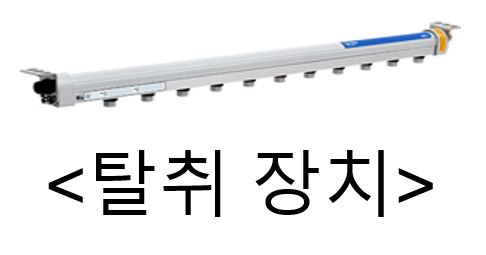
research/탈취 장치.JPG
