polygm/cat_2022/research/판형 사진.JPG

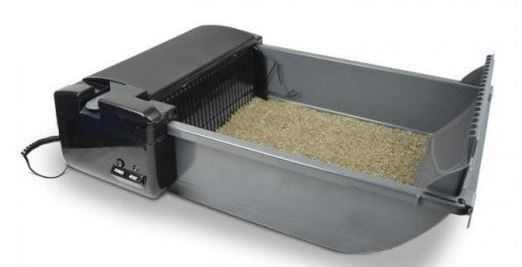
research/판형 사진.JPG
