polygm/cat_2022/research/판형 어플.JPG

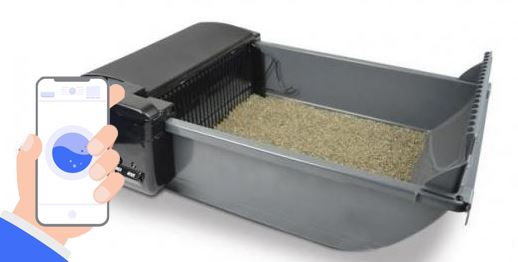
research/판형 어플.JPG
