polygm/cat_2022/research/팬모터.JPG

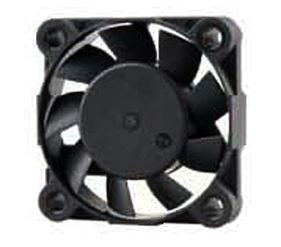
research/팬모터.JPG
