polygm/cat_2022/research/펀딩.JPG

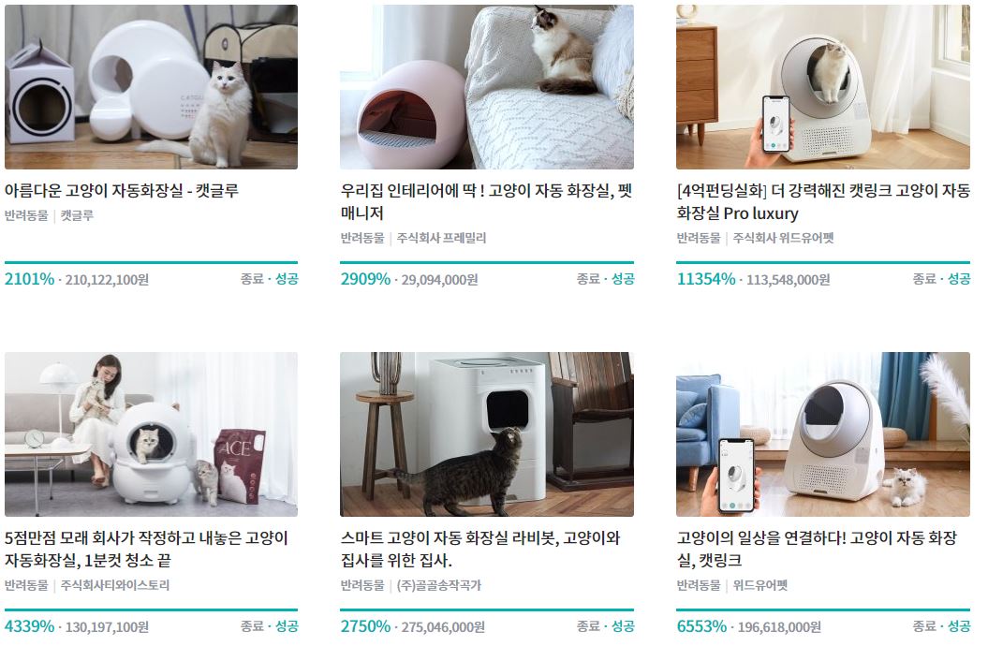
research/펀딩.JPG
