polygm/cat_2022/research/함축.JPG

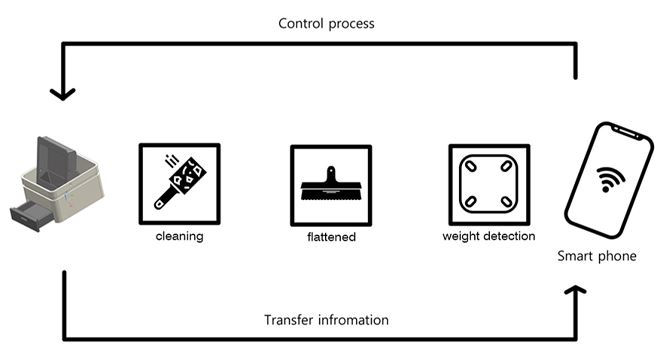
research/함축.JPG
