polygm/cat_2022/research/현황.JPG

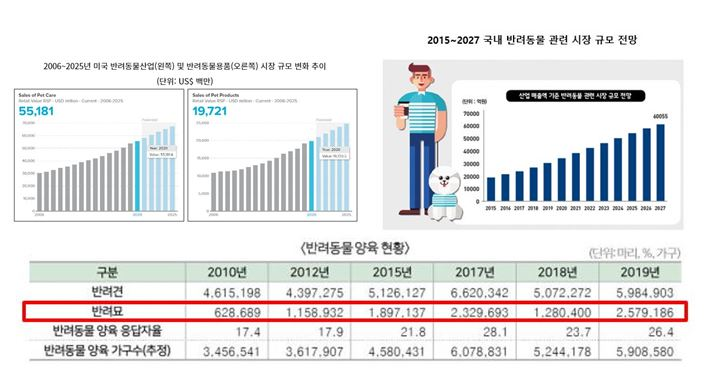
research/현황.JPG
