polygm/cat_2022/research/흐름도.jpg

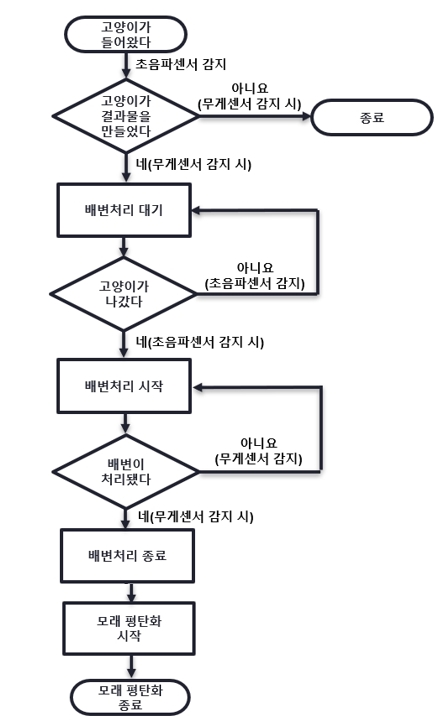
research/흐름도.jpg
