polygm/cat_2022/modeling/컴포넌트/ㅇ/Ultrasonic Sensor HC-SR04/hc-sr04 part5.SLDPRT

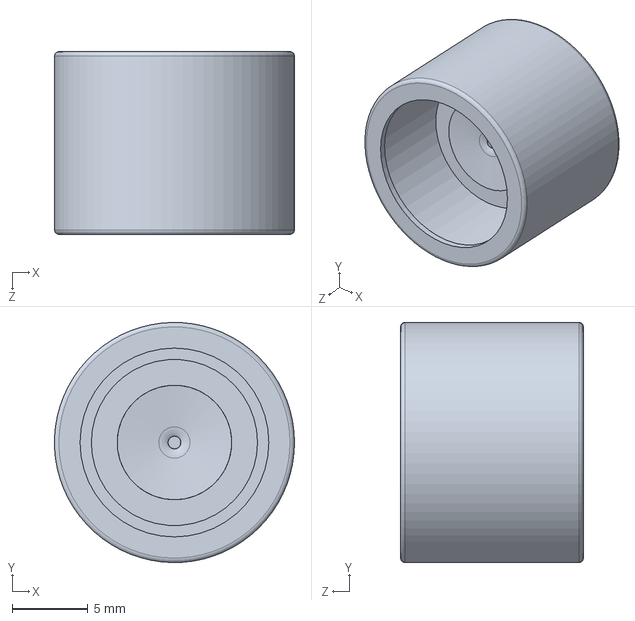
[picture p230: CAD file, 2022-10-05]
modeling/컴포넌트/ㅇ/Ultrasonic Sensor HC-SR04/hc-sr04 part5.SLDPRT
15.9 x 15.9 x 12.1 mm
