polygm/cat_2022/modeling/컴포넌트/ㅇ/Ultrasonic Sensor HC-SR04/SMD resistor.SLDPRT

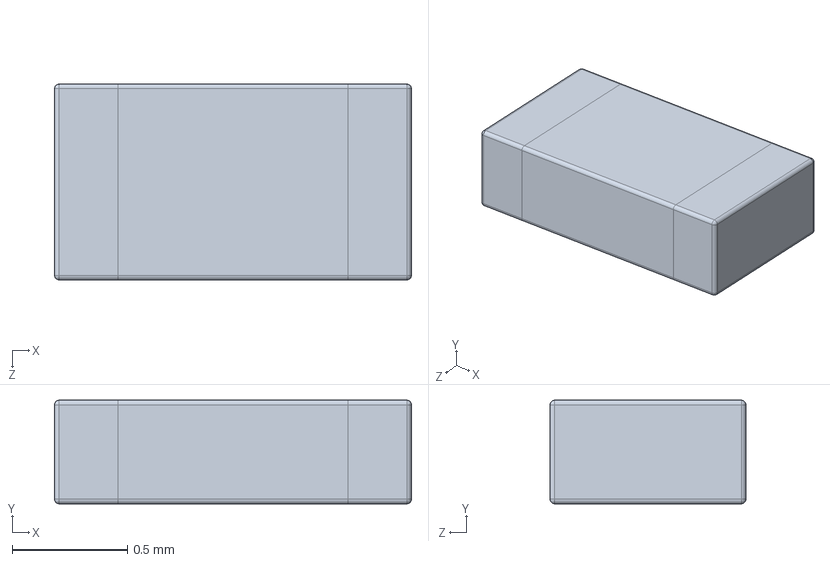
[picture p231: CAD file, 2022-10-05]
modeling/컴포넌트/ㅇ/Ultrasonic Sensor HC-SR04/SMD resistor.SLDPRT
1.55 x 0.45 x 0.85 mm
