polygm/cat_2022/modeling/컴포넌트/ㅇ/Ultrasonic Sensor HC-SR04/hc-sr04 part7.SLDPRT

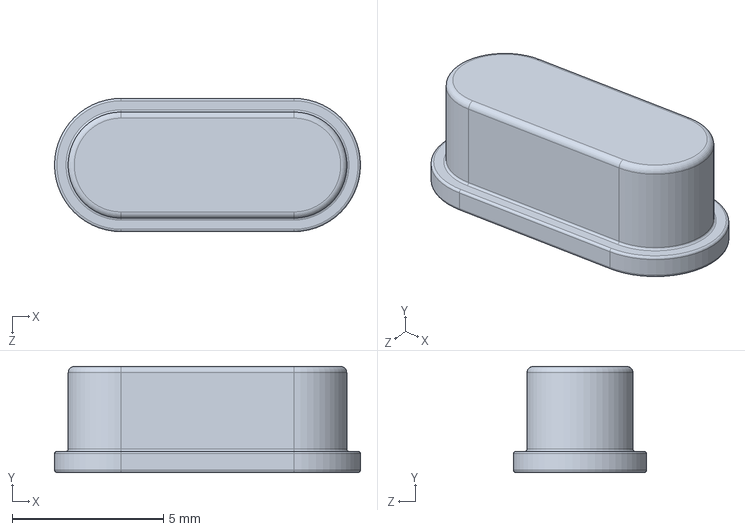
[picture p232: CAD file, 2022-10-05]
modeling/컴포넌트/ㅇ/Ultrasonic Sensor HC-SR04/hc-sr04 part7.SLDPRT
10.1 x 3.50 x 4.40 mm
