polygm/cat_2022/modeling/컴포넌트/ㅇ/Ultrasonic Sensor HC-SR04/hc-sr04 part6.SLDPRT

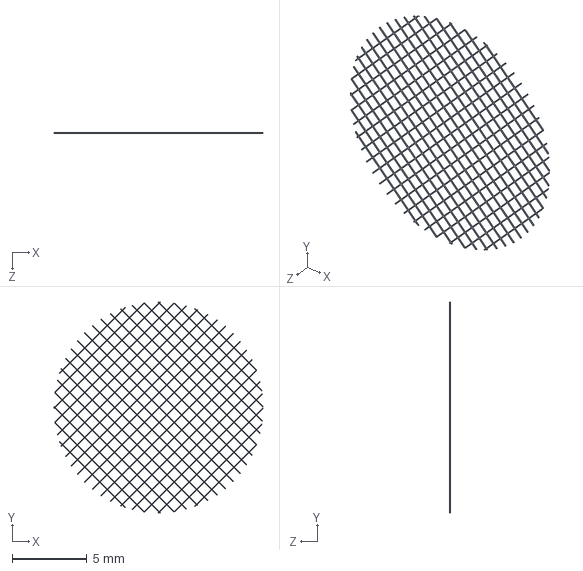
[picture p233: CAD file, 2022-10-05]
modeling/컴포넌트/ㅇ/Ultrasonic Sensor HC-SR04/hc-sr04 part6.SLDPRT
14.0 x 14.1 x 0.05 mm
